Khaiduy/Open8_PCB/Open8_Epaper_demo_PCB/Pin_Assignment_RS6521_1_.xlsx

Sheet: Index
Index |  |  | 2021-11-05
No. | Sheet | Contents | Note
1 | Index | Table of contents of this Excel file | This sheet
2 | History | Modified history of this Excel file
3 | Chip Allocation | Chip Allocation
4 | Pin Assignment R4250 | Pin Assignment for R4250
5 | Pin Assignment R4251 | Pin Assignment for R4251
6 | Pin Assignment R4252 | Pin Assignment for R4252
7 | Circuit Layout | Circuit Layout
8 | IO Description | Description of I/O Pins

Sheet: History
Back to Index
 | Modified History
 | No. | Date | Modified by | Sheet | Updates | Note
 | 1 | 2017-06-15 | Hotta | All | New created
 | 2 | 2017-06-25 | Hotta | Chip Allocation Pin Assignment R4252 | Relocated HU_RISC16 => HU_FLOATW & HU_DCT32
 | 3 | 2017-06-26 | Hotta | Pin Assignment R4252 | No.74 => Unused
 | 4 | 2017-07-03 | Hotta | Pin Assignment R4252 | All pins have been relocated.
 | 5 | 2017-07-06 | Hotta | Pin Assignment R4252 | Common digital input pins have been assigned.
 | 6 | 2017-07-07 | Hotta | Pin Assignment R4252 | Relocated due to the cancellation of AESCOM.
 | 7 | 2017-07-07 | Hotta | Pin Assignment R4252 | Bug fix (No.12, 62, 82).
 | 8
 | 9
 | 10
 | 11
 | 12
 | 13
 | 14
 | 15
 | 16
 | 17
 | 18
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
