Khaiduy/Open8_PCB/PCB_20PIN_PMOD_ADAPTER/JTAG_PMOD_ADAPTER.png

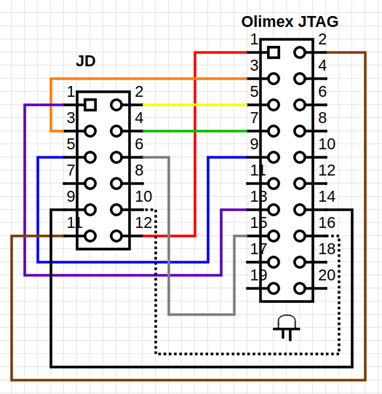
PCB_20PIN_PMOD_ADAPTER/JTAG_PMOD_ADAPTER.png
