Khaiduy/Open8_PCB/PCB_20PIN_PMOD_ADAPTER/Pmod_to_JTAG_bottom.png

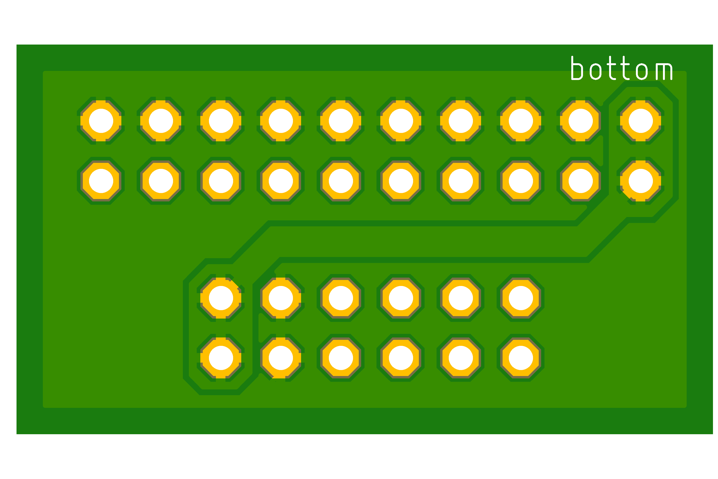
PCB_20PIN_PMOD_ADAPTER/Pmod_to_JTAG_bottom.png
