Khaiduy/Open8_PCB/PCB_20PIN_PMOD_ADAPTER/Pmod_to_JTAG_top.png

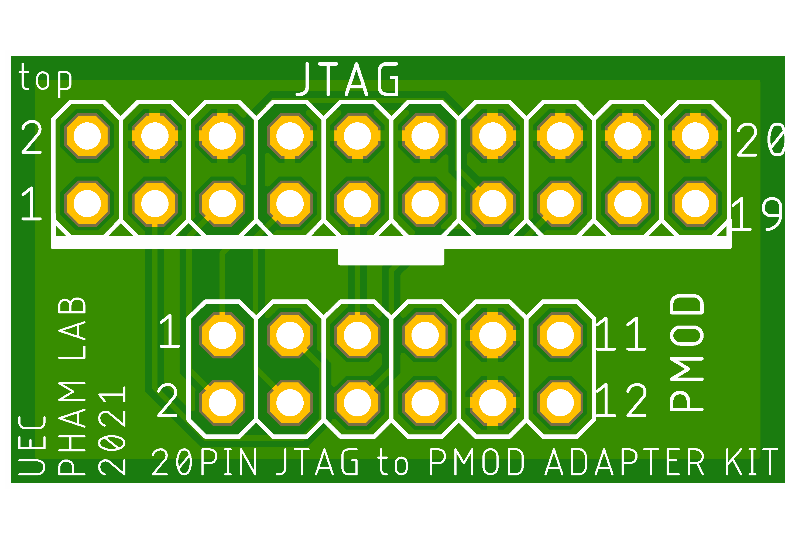
PCB_20PIN_PMOD_ADAPTER/Pmod_to_JTAG_top.png
