Khaiduy/Open8_PCB/PCB_ROHM_BaAnh/PCB_ROHM_BaAnh_bottom.png

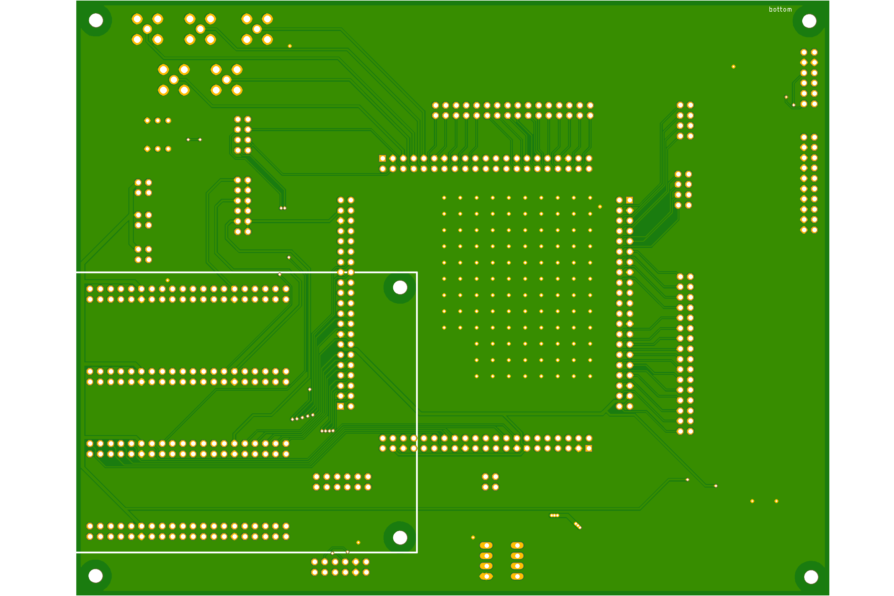
PCB_ROHM_BaAnh/PCB_ROHM_BaAnh_bottom.png
