Khaiduy/Open8_PCB/QFP160_new_socket/qfp160_socket_new_bottom.png

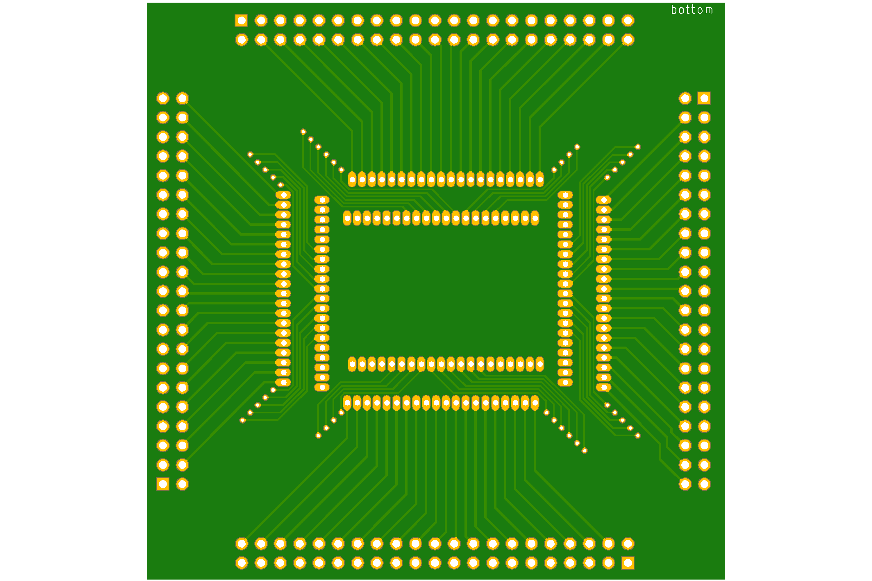
QFP160_new_socket/qfp160_socket_new_bottom.png
