Khaiduy/Open8_PCB/SERV_Open8_SOTB_PCB/serv_open8_sotb_bottom.png

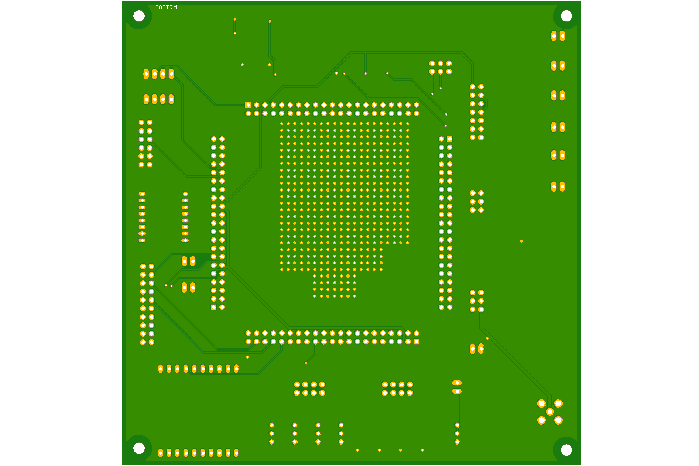
SERV_Open8_SOTB_PCB/serv_open8_sotb_bottom.png
