Khaiduy/Open8_PCB/TR4_PGA257(v4.0)/TR4.pdf

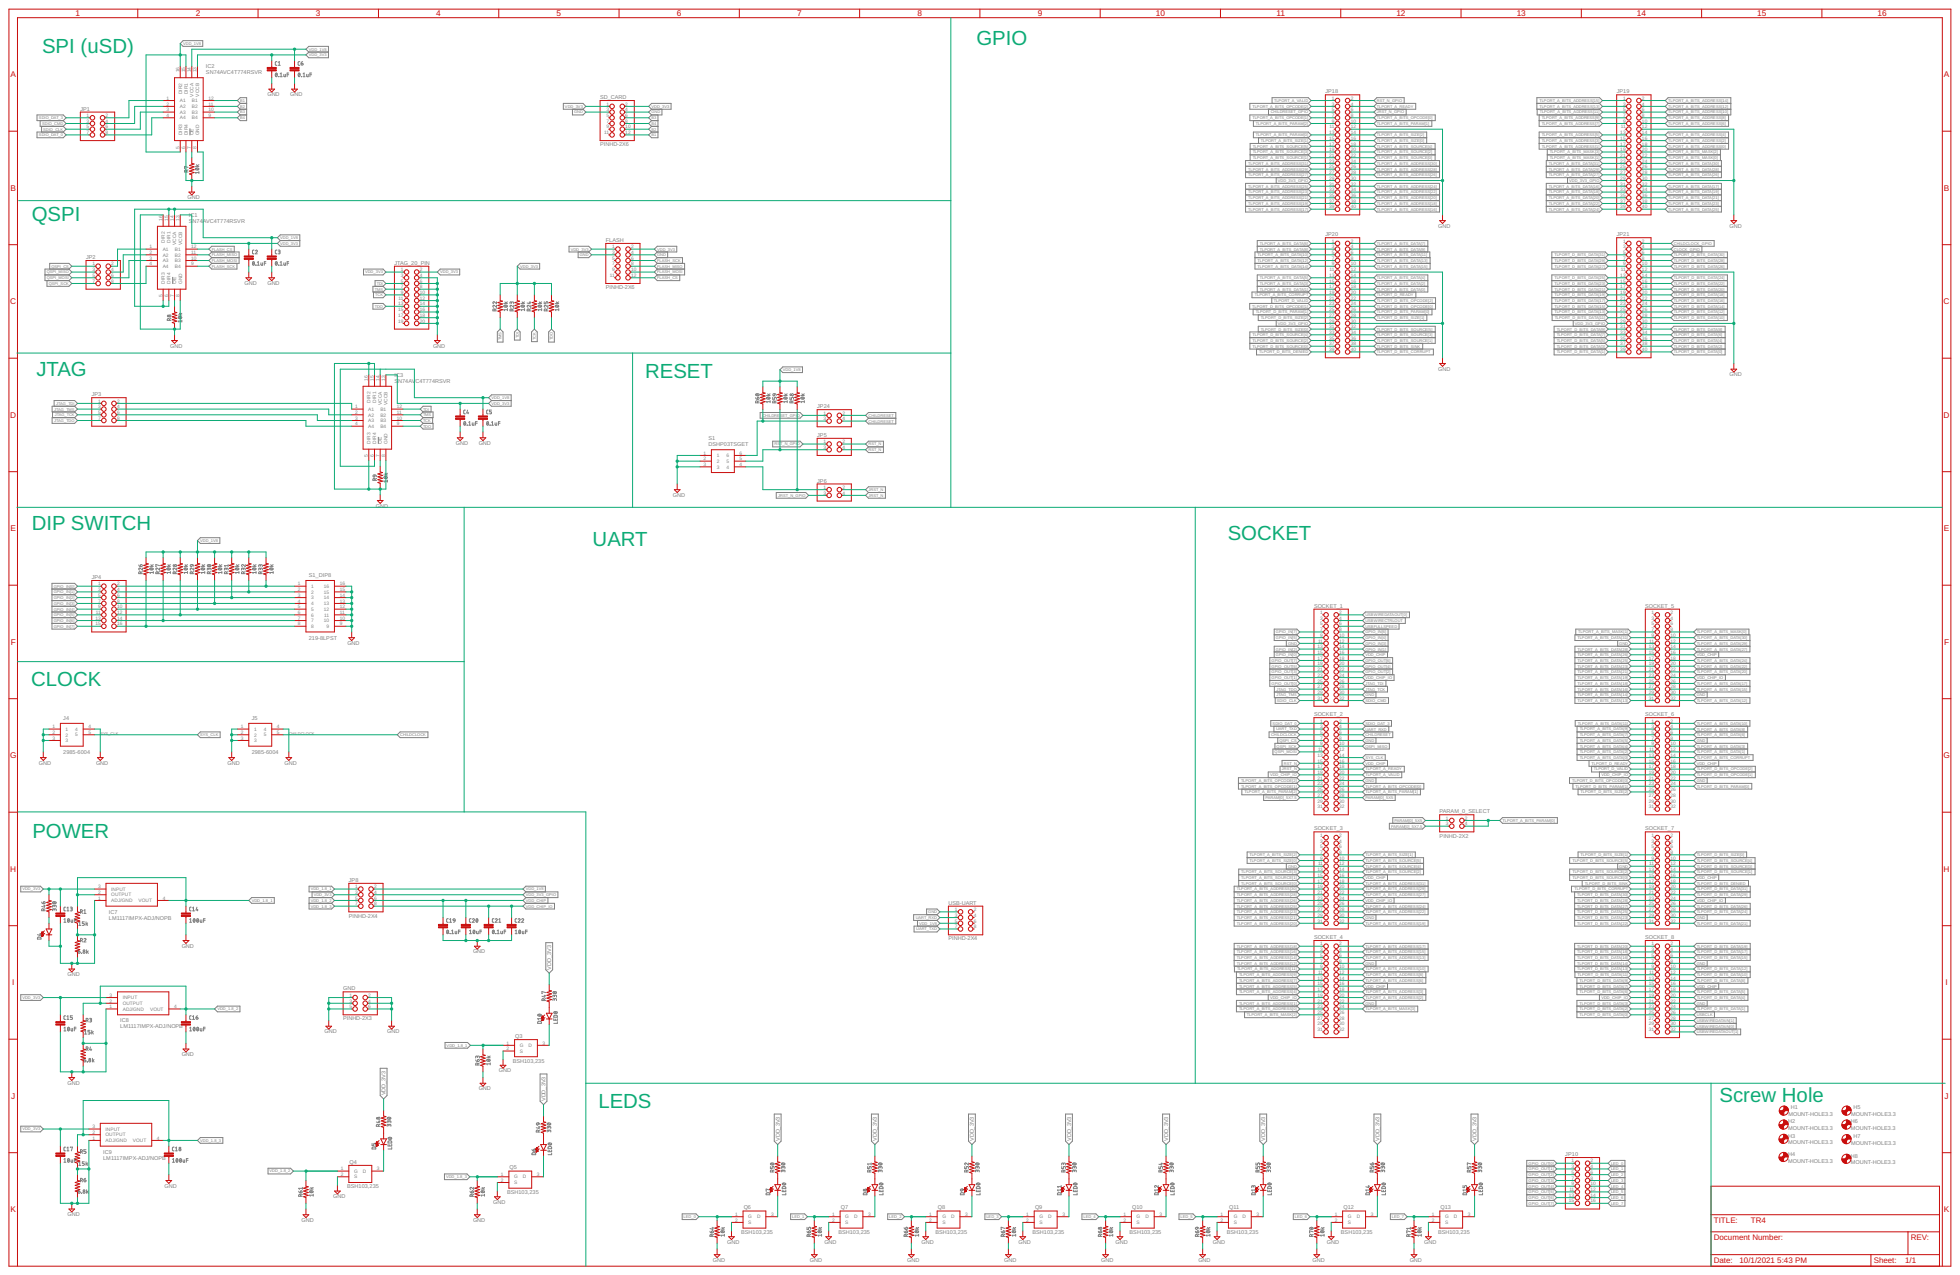
[picture p20: page 1]

MOUNT-HOLE3.3 MOUNT-HOLE3.3
