Khaiduy/Open8_PCB/SERV_Open8_TSMC_PCB/serv_open8_tsmc.pdf

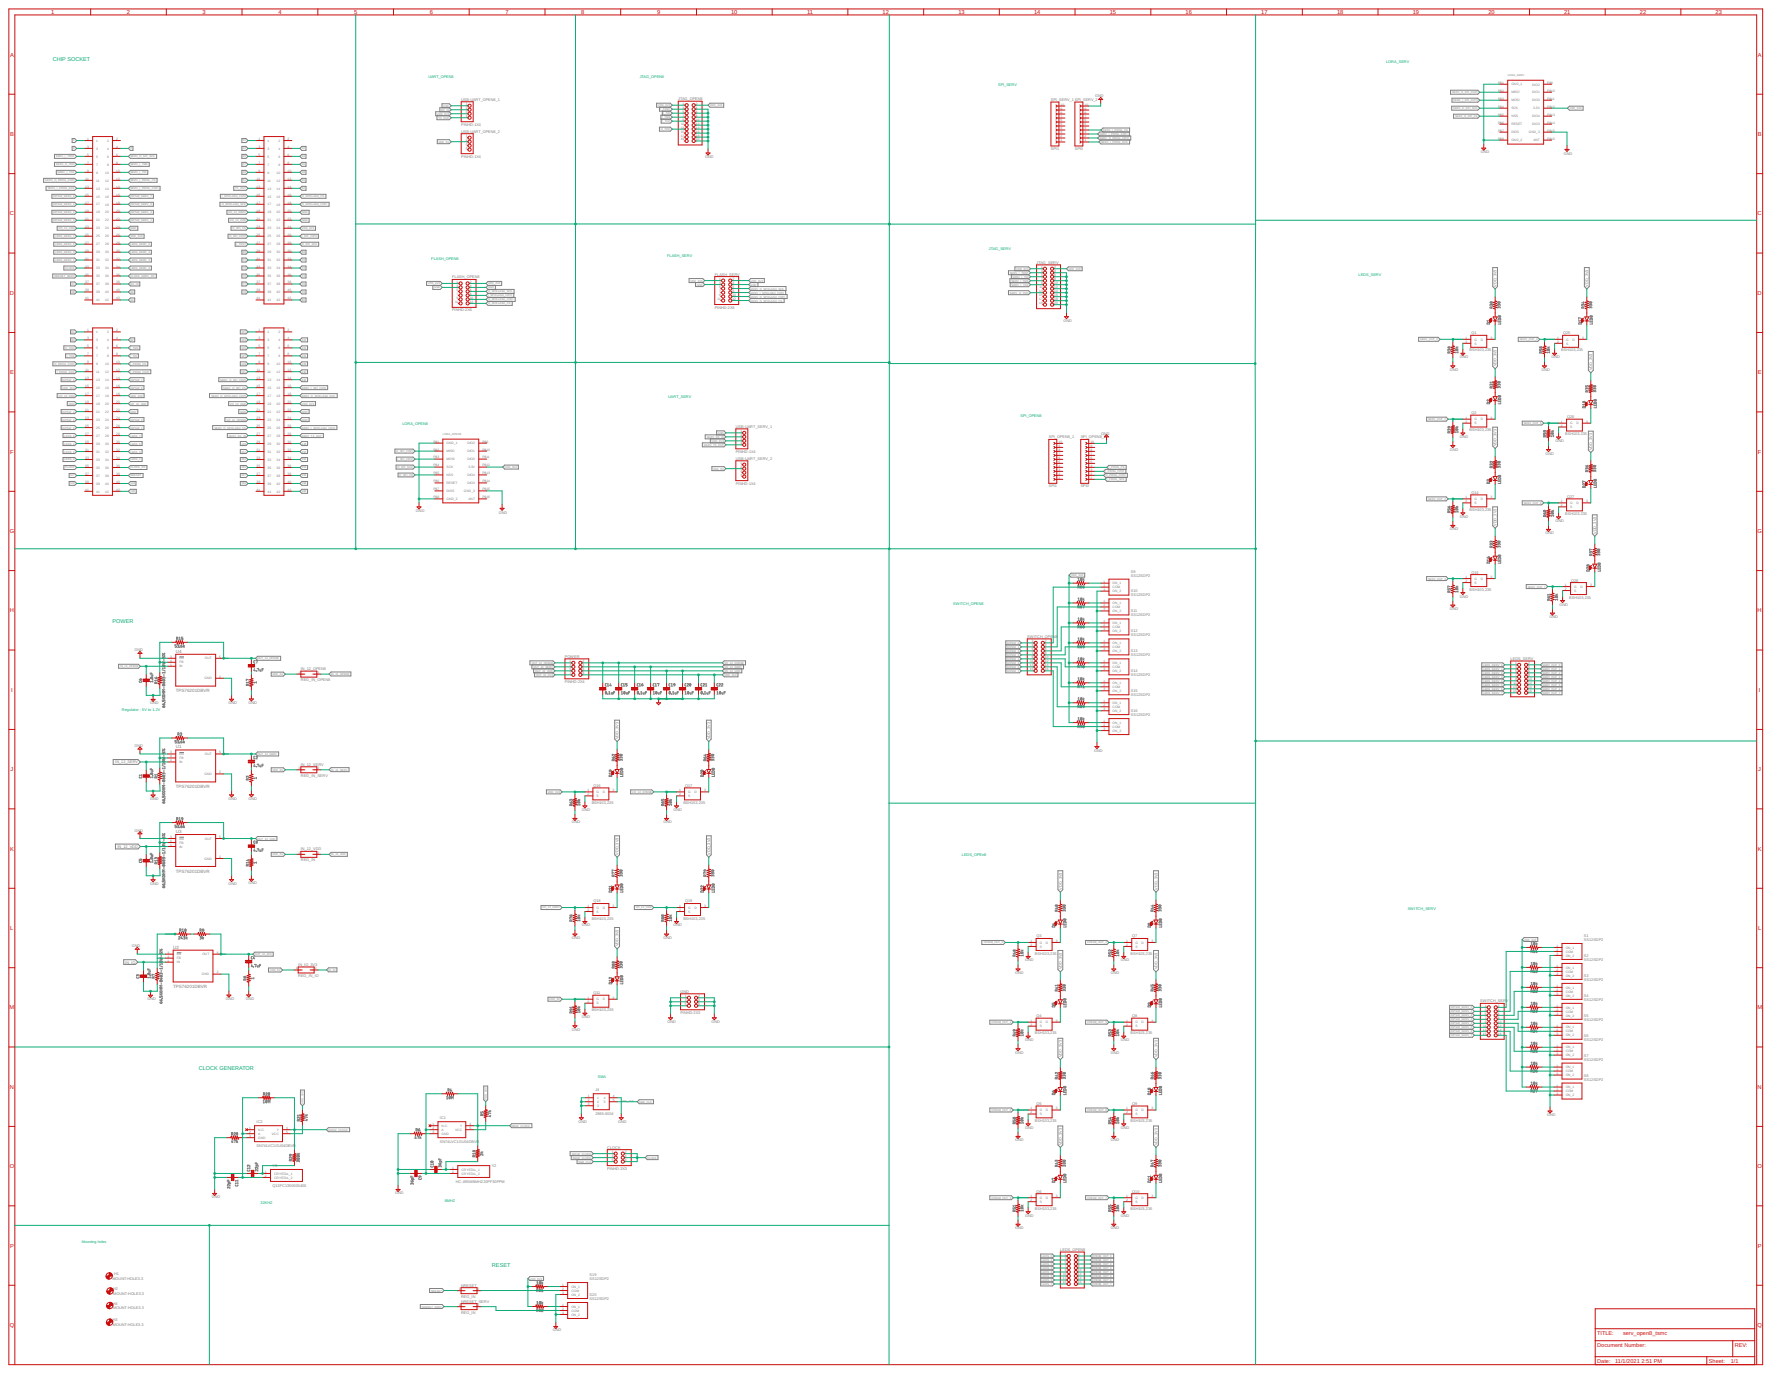
[picture p24: page 1]
