Khaiduy/Open8_PCB/TR4_PGA257(v4.0)/TEE_PGA257_v3.0.pdf

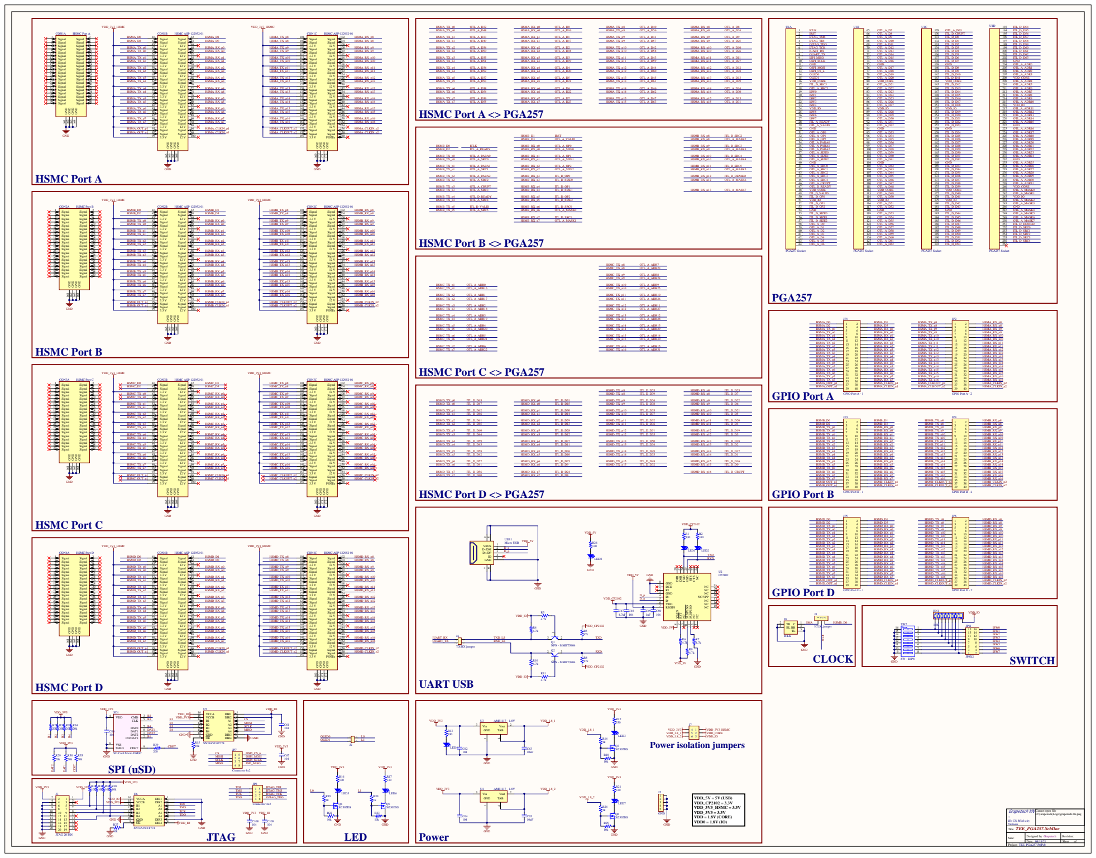
[picture p25: page 1]

NC 22 CTS 23 RTS 24 RXD 25 TXD 26 DSR 27 DTR 28

Cannot open file
D:\Grapetech\Logo\grapetech-06.png

Date: 04/19/21 | Sheet of
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
