Khaiduy/Open8_PCB/SERV_Open8_TSMC_PCB/serv_open8_tsmc.brd

## EAGLE design SERV_Open8_TSMC_PCB/serv_open8_tsmc.brd (2021-11-15)

Schematic: serv_open8_tsmc.sch

Parts:
C1, C3, C5, C6: 1.0uF; 0603
C2, C4, C7, C8: 4.7uF; 0603
C9, C10: 36pF; 0603
C11, C12: 22pF; 0603
C14, C16, C19, C21: 0.1uF; 0603
C15, C17, C20, C22: 10uF; 0603
CLOCK: PINHD-2X3; 2X03
D1, D2, D3, D4, D5, D6, D7, D8, D9, D10, D11, D12, D16, D17, D18, D19, D20, D21, D22, D27, D28: LED0; LED-0603
FLASH_OPEN8: PINHD-2X6; 2X06
FLASH_SERV: PINHD-2X6; 2X06
GND: PINHD-2X3; 2X03
H1, H2, H3, H4: MOUNT-HOLE3.3; 3,3
IC1, IC2: SN74LVC1GU04DBVR; SOT95P280X145-5N
IN_12_OPEN8: REG_IN_OPEN8; JP1
IN_12_SERV: REG_IN_SERV; JP1
IN_12_VDD: REG_IN; JP1
IN_IO_3V3: REG_IN_IO; JP1
J4: 2985-6004; 29856004
JTAG_OPEN8: PINHD-2X10; 2X10
JTAG_SERV: PINHD-2X10; 2X10
LEDS_OPEN8: PINHD-2X8; 2X08
LEDS_SERV: PINHD-2X8; 2X08
LORA_OPEN8: RFM95W-915S2; RFM95-915S2
LORA_SERV: RFM95W-915S2; RFM95-915S2
NRESET: REG_IN; JP1
NRESET_SERV: REG_IN; JP1
POWER: PINHD-2X4; 2X04
Q1, Q2, Q3, Q4, Q5, Q6, Q7, Q8, Q9, Q10, Q11, Q14, Q15, Q16, Q17, Q18, Q19, Q25, Q26, Q27, Q28: BSH103,235; SOT95P230X110-3N
R1, R7, R13, R16: 66.5KOHM-0603-1/10W-5%; 0603
R2, R8, R14, R17: 1; 0603
R3, R15, R19: 53.6k; 0603
R4, R20: 10M; 0603
R5, R6, R21, R28: 47k; 0603
R9: 3k; 0603
R10: 243k; 0603
R11, R12, R22, R23, R24, R25, R26, R27, R38, R39, R48, R49, R50, R51, R52, R53, R54, R55, R56, R57, R58, R59, R60, R61, R63, R65, R66, R67, R68, R69, R70, R71, R78, R80, R81, R82, R89, R90, R91: 10k; 0603
R18: 2k; 0603
R29: 300k; 0603
R30, R31, R32, R33, R34, R35, R36, R37, R40, R41, R42, R43, R44, R45, R46, R47, R62, R64, R77, R79, R88: 330; 0603
S1, S2, S3, S4, S5, S6, S7, S8, S9, S10, S11, S12, S13, S14, S15, S16, S19, S20: SS12SDP2
SPI_OPEN8_1: SPI1; FE10
SPI_OPEN8_2: SPI0; FE10
SPI_SERV_1: SPI1; FE10
SPI_SERV_2: SPI0; FE10
SWITCH_OPEN8: PINHD-2X8; 2X08
SWITCH_SERV: PINHD-2X8; 2X08
U1, U2, U3, U4: TPS76201DBVR; SOT95P280X145-5N
U$1, U$2, U$3, U$4: 2X41_HEADER
USB-UART_OPEN8_1, USB-UART_OPEN8_2: PINHD-1X4; 1X04
USB-UART_SERV_1, USB-UART_SERV_2: PINHD-1X4; 1X04
Y2: HC-49SM8MHZ20PF30PPM; HC49SM8MHZ20PF30PPM
Y3: Q13FC1350000400

Connections:
1: U$1.1
2: U$1.4
3: U$1.3
8MHZ_CLOCK: CLOCK.3, IC1.4 (Y), R4.2, R18.2
32KHZ_CLOCK: CLOCK.1, IC2.4 (Y), R20.2, R29.2
37: U$1.37
38: U$1.40
39: U$1.39
40: U$1.42
41: U$2.1
42: U$2.4
43: U$2.3
44: U$2.6
45: U$2.5
46: U$2.8
47: U$2.7
48: U$2.10
49: U$2.9
50: U$2.12
51: U$2.11
52: U$2.14
68: U$2.30
69: U$2.29
70: U$2.32
71: U$2.31
72: U$2.34
73: U$2.33
74: U$2.36
75: U$2.35
76: U$2.38
77: U$2.37
78: U$2.40
79: U$2.39
80: U$2.42
81: U$3.1
82: U$3.4
83: U$3.3
117: U$3.37
118: U$3.40
119: U$3.39
120: U$3.42
121: U$4.1
122: U$4.4
123: U$4.3
124: U$4.6
125: U$4.5
126: U$4.8
127: U$4.7
128: U$4.10
129: U$4.9
130: U$4.12
131: U$4.11
132: U$4.14
148: U$4.30
149: U$4.29
150: U$4.32
151: U$4.31
152: U$4.34
153: U$4.33
154: U$4.36
155: U$4.35
156: U$4.38
157: U$4.37
158: U$4.40
159: U$4.39
160: U$4.42
CLOCK: CLOCK.2, CLOCK.4, CLOCK.6, U$1.33, U$3.35
CLOCK_SERV_XO: U$1.36
CLOCK_XO: U$3.36
DIPSW_0: SWITCH_OPEN8.1, U$3.25
DIPSW_1: SWITCH_OPEN8.3, U$3.26
DIPSW_2: SWITCH_OPEN8.5, U$3.23
DIPSW_3: SWITCH_OPEN8.7, U$3.24
DIPSW_4: SWITCH_OPEN8.9, U$3.21
DIPSW_5: SWITCH_OPEN8.11, U$3.16
DIPSW_6: SWITCH_OPEN8.13, U$3.13
DIPSW_7: SWITCH_OPEN8.15, U$3.14
DIPSW_SERV_0: SWITCH_SERV.1, U$1.21
DIPSW_SERV_1: SWITCH_SERV.3, U$1.22
DIPSW_SERV_2: SWITCH_SERV.5, U$1.19
DIPSW_SERV_3: SWITCH_SERV.7, U$1.20
DIPSW_SERV_4: SWITCH_SERV.9, U$1.17
DIPSW_SERV_5: SWITCH_SERV.11, U$1.18
DIPSW_SERV_6: SWITCH_SERV.13, U$1.15
DIPSW_SERV_7: SWITCH_SERV.15, U$1.16
GND: C1.2, C3.2, C5.2, C6.2, C9.2, C10.1, C11.2, C12.1, C14.2, C15.2, C16.2, C17.2, C19.2, C20.2, C21.2, C22.2, FLASH_OPEN8.3, FLASH_OPEN8.4, FLASH_SERV.3, FLASH_SERV.4, GND.1, GND.2, GND.3, GND.4, GND.5, GND.6, J4.1, J4.2, J4.3, J4.4, JTAG_OPEN8.4, JTAG_OPEN8.6, JTAG_OPEN8.8, JTAG_OPEN8.10, JTAG_OPEN8.12, JTAG_OPEN8.14, JTAG_OPEN8.16, JTAG_OPEN8.18, JTAG_OPEN8.20, JTAG_SERV.4, JTAG_SERV.6, JTAG_SERV.8, JTAG_SERV.10, JTAG_SERV.12, JTAG_SERV.14, JTAG_SERV.16, JTAG_SERV.18, JTAG_SERV.20, LORA_OPEN8.P$1 (GND_1), LORA_OPEN8.P$8 (GND_2), LORA_OPEN8.P$15 (GND_3), LORA_SERV.P$1 (GND_1), LORA_SERV.P$8 (GND_2), LORA_SERV.P$15 (GND_3), Q1.2 (S), Q2.2 (S), Q3.2 (S), Q4.2 (S), Q5.2 (S), Q6.2 (S), Q7.2 (S), Q8.2 (S), Q9.2 (S), Q10.2 (S), Q11.2 (S), Q14.2 (S), Q15.2 (S), Q16.2 (S), Q17.2 (S), Q18.2 (S), Q19.2 (S), Q25.2 (S), Q26.2 (S), Q27.2 (S), Q28.2 (S), R1.1, R2.1, R6.1, R7.1, R8.1, R13.1, R14.1, R16.1, R17.1, R28.1, R38.1, R39.1, R48.1, R49.1, R50.1, R51.1, R52.1, R53.1, R54.1, R55.1, R56.1, R57.1, R58.1, R59.1, R60.1, R61.1, R63.1, R65.1, R78.1, R80.1, R91.1, S1.3 (ON_2), S2.3 (ON_2), S3.3 (ON_2), S4.3 (ON_2), S5.3 (ON_2), S6.3 (ON_2), S7.3 (ON_2), S8.3 (ON_2), S9.3 (ON_2), S10.3 (ON_2), S11.3 (ON_2), S12.3 (ON_2), S13.3 (ON_2), S14.3 (ON_2), S15.3 (ON_2), S16.3 (ON_2), S19.3 (ON_2), S20.3 (ON_2), SPI_OPEN8_2.10, SPI_SERV_2.10, U1.2 (GND), U1.3 (!EN), U2.2 (GND), U2.3 (!EN), U3.2 (GND), U3.3 (!EN), U4.2 (GND), U4.3 (!EN), U$1.24, U$2.20, U$2.22, U$3.19, U$3.22, U$4.21, U$4.22, U$4.24, USB-UART_OPEN8_1.1, USB-UART_SERV_1.1
IN_12_OPEN8: C6.1, IN_12_OPEN8.2, U4.1 (IN)
IN_12_SERV: C1.1, IN_12_SERV.2, U1.1 (IN)
IN_12_VDD: C5.1, IN_12_VDD.2, U3.1 (IN)
IN_IO: C3.1, IN_IO_3V3.2, U2.1 (IN)
I_PROG_COPI: SPI_OPEN8_2.3, U$3.12
I_PROG_CS: SPI_OPEN8_2.4, U$3.10
I_PROG_SCK: SPI_OPEN8_2.1, U$3.11
I_SPIFLASH_CIPO: FLASH_OPEN8.8, U$2.15
I_SPI_CIPO: LORA_OPEN8.P$3 (MOSI), U$2.26
I_TCK: JTAG_OPEN8.9, U$3.7
I_TDI: JTAG_OPEN8.5, U$3.8
I_TMS: JTAG_OPEN8.7, U$3.6
I_TRST: JTAG_OPEN8.3, U$2.27
LEDS_0: LEDS_OPEN8.1, U$3.33
LEDS_1: LEDS_OPEN8.3, U$3.34
LEDS_2: LEDS_OPEN8.5, U$3.31
LEDS_3: LEDS_OPEN8.7, U$3.32
LEDS_4: LEDS_OPEN8.9, U$3.29
LEDS_5: LEDS_OPEN8.11, U$3.30
LEDS_6: LEDS_OPEN8.13, U$3.27
LEDS_7: LEDS_OPEN8.15, U$3.28
LEDS_SERV_0: LEDS_SERV.1, U$1.34
LEDS_SERV_1: LEDS_SERV.3, U$1.31
LEDS_SERV_2: LEDS_SERV.5, U$1.32
LEDS_SERV_3: LEDS_SERV.7, U$1.29
LEDS_SERV_4: LEDS_SERV.9, U$1.30
LEDS_SERV_5: LEDS_SERV.11, U$1.27
LEDS_SERV_6: LEDS_SERV.13, U$1.28
LEDS_SERV_7: LEDS_SERV.15, U$1.25
unnamed: R1.2, R3.1, U1.4 (FB)
unnamed: C2.2, R2.2
unnamed: NRESET.2, S19.2 (COM)
unnamed: IC1.3 (GND), R6.2
unnamed: C9.1, IC1.2 (A), R4.1, Y2.2 (CRYSTAL_2)
unnamed: R7.2, R10.1, U2.4 (FB)
unnamed: C4.2, R8.2
unnamed: R9.1, R10.2
unnamed: C10.2, R18.1, Y2.1 (CRYSTAL_1)
unnamed: R11.1, S1.1 (ON_1)
unnamed: R12.1, S2.1 (ON_1)
unnamed: R13.2, R19.1, U3.4 (FB)
unnamed: C8.2, R14.2
unnamed: IC1.5 (VCC), R5.1
unnamed: D12.A, R88.1
unnamed: R22.1, S3.1 (ON_1)
unnamed: R23.1, S4.1 (ON_1)
unnamed: R24.1, S5.1 (ON_1)
unnamed: R25.1, S6.1 (ON_1)
unnamed: R26.1, S7.1 (ON_1)
unnamed: R27.1, S8.1 (ON_1)
unnamed: S5.2 (COM), SWITCH_SERV.10
unnamed: S6.2 (COM), SWITCH_SERV.12
unnamed: S7.2 (COM), SWITCH_SERV.14
unnamed: S8.2 (COM), SWITCH_SERV.16
unnamed: S4.2 (COM), SWITCH_SERV.8
unnamed: S3.2 (COM), SWITCH_SERV.6
unnamed: S2.2 (COM), SWITCH_SERV.4
unnamed: S1.2 (COM), SWITCH_SERV.2
unnamed: R15.1, R16.2, U4.4 (FB)
unnamed: IC2.3 (GND), R28.2
unnamed: C7.2, R17.2
unnamed: C11.1, IC2.2 (A), R20.1, Y3.2 (CRYSTAL_2)
unnamed: C12.2, R29.1, Y3.1 (CRYSTAL_1)
unnamed: NRESET_SERV.2, S20.2 (COM)
unnamed: IC2.5 (VCC), R21.1
unnamed: D1.A, R30.1
unnamed: D1.C, Q1.3 (D)
unnamed: D2.A, R31.1
unnamed: D2.C, Q2.3 (D)
unnamed: R81.1, S19.1 (ON_1)
unnamed: R82.1, S20.1 (ON_1)
unnamed: D12.C, Q11.3 (D)
unnamed: D3.A, R32.1
unnamed: D3.C, Q14.3 (D)
unnamed: D4.A, R40.1
unnamed: D4.C, Q3.3 (D)
unnamed: D5.A, R41.1
unnamed: D16.A, R33.1
unnamed: D16.C, Q15.3 (D)
unnamed: D17.A, R34.1
unnamed: D17.C, Q25.3 (D)
unnamed: D18.A, R35.1
unnamed: D18.C, Q26.3 (D)
unnamed: D27.A, R36.1
unnamed: D27.C, Q27.3 (D)
unnamed: D28.A, R37.1
unnamed: D28.C, Q28.3 (D)
unnamed: D19.A, R62.1
unnamed: D5.C, Q4.3 (D)
unnamed: D6.A, R42.1
unnamed: D6.C, Q5.3 (D)
unnamed: D7.A, R43.1
unnamed: D7.C, Q6.3 (D)
unnamed: D8.A, R44.1
unnamed: D8.C, Q7.3 (D)
unnamed: D9.A, R45.1
unnamed: D19.C, Q16.3 (D)
unnamed: D20.A, R64.1
unnamed: D20.C, Q17.3 (D)
unnamed: D21.A, R77.1
unnamed: D21.C, Q18.3 (D)
unnamed: D22.A, R79.1
unnamed: D22.C, Q19.3 (D)
unnamed: D9.C, Q8.3 (D)
unnamed: D10.A, R46.1
unnamed: D10.C, Q9.3 (D)
unnamed: D11.A, R47.1
unnamed: D11.C, Q10.3 (D)
unnamed: R66.1, S9.1 (ON_1)
unnamed: R67.1, S10.1 (ON_1)
unnamed: R68.1, S11.1 (ON_1)
unnamed: R69.1, S12.1 (ON_1)
unnamed: R70.1, S13.1 (ON_1)
unnamed: R71.1, S14.1 (ON_1)
unnamed: R89.1, S15.1 (ON_1)
unnamed: R90.1, S16.1 (ON_1)
unnamed: S13.2 (COM), SWITCH_OPEN8.10
unnamed: S14.2 (COM), SWITCH_OPEN8.12
unnamed: S15.2 (COM), SWITCH_OPEN8.14
unnamed: S16.2 (COM), SWITCH_OPEN8.16
unnamed: S12.2 (COM), SWITCH_OPEN8.8
unnamed: S11.2 (COM), SWITCH_OPEN8.6
unnamed: S10.2 (COM), SWITCH_OPEN8.4
unnamed: S9.2 (COM), SWITCH_OPEN8.2
NRESET: NRESET.1, U$3.38
NRESET_SERV: NRESET_SERV.1, U$1.35
OPEN8_OUT_0: LEDS_OPEN8.2, Q3.1 (G), R48.2
OPEN8_OUT_1: LEDS_OPEN8.4, Q4.1 (G), R49.2
OPEN8_OUT_2: LEDS_OPEN8.6, Q5.1 (G), R50.2
OPEN8_OUT_3: LEDS_OPEN8.8, Q6.1 (G), R51.2
OPEN8_OUT_4: LEDS_OPEN8.10, Q7.1 (G), R52.2
OPEN8_OUT_5: LEDS_OPEN8.12, Q8.1 (G), R53.2
OPEN8_OUT_6: LEDS_OPEN8.14, Q9.1 (G), R54.2
OPEN8_OUT_7: LEDS_OPEN8.16, Q10.1 (G), R55.2
OUT_12_OPEN8: C7.1, POWER.1, R15.2, U4.5 (OUT)
OUT_12_SERV: C2.1, POWER.3, R3.2, U1.5 (OUT)
OUT_12_VDD: C8.1, POWER.5, R19.2, U3.5 (OUT)
OUT_IO_3V3: C4.1, POWER.7, R9.2, U2.5 (OUT)
O_PROG_CIPO: SPI_OPEN8_2.2, U$3.9
O_SPIFLASH_COPI: FLASH_OPEN8.10, U$2.18
O_SPIFLASH_CS: FLASH_OPEN8.12, U$2.16
O_SPIFLASH_SCK: FLASH_OPEN8.6, U$2.17
O_SPI_COPI: LORA_OPEN8.P$2 (MISO), U$2.25
O_SPI_CS: LORA_OPEN8.P$5 (NSS), U$2.23
O_SPI_SCK: LORA_OPEN8.P$4 (SCK), U$2.28
O_TDO: JTAG_OPEN8.13, U$3.5
RX_IN: U$1.38, USB-UART_OPEN8_1.2
SERV_I_PROG_COPI: SPI_SERV_2.3, U$1.14
SERV_I_PROG_CS: SPI_SERV_2.4, U$1.12
SERV_I_PROG_SCK: SPI_SERV_2.1, U$1.13
SERV_I_SPIFLASH_CIPO: FLASH_SERV.8, U$4.26
SERV_I_SPI_CIPO: LORA_SERV.P$3 (MOSI), U$4.16
SERV_I_TCK: JTAG_SERV.9, U$1.9
SERV_I_TDI: JTAG_SERV.5, U$1.10
SERV_I_TMS: JTAG_SERV.7, U$1.8
SERV_I_TRST: JTAG_SERV.3, U$1.5
SERV_OUT_0: LEDS_SERV.2, Q1.1 (G), R38.2
SERV_OUT_1: LEDS_SERV.4, Q2.1 (G), R39.2
SERV_OUT_2: LEDS_SERV.6, Q14.1 (G), R56.2
SERV_OUT_3: LEDS_SERV.8, Q15.1 (G), R57.2
SERV_OUT_4: LEDS_SERV.10, Q25.1 (G), R58.2
SERV_OUT_5: LEDS_SERV.12, Q26.1 (G), R59.2
SERV_OUT_6: LEDS_SERV.14, Q27.1 (G), R60.2
SERV_OUT_7: LEDS_SERV.16, Q28.1 (G), R61.2
SERV_O_PROG_CIPO: SPI_SERV_2.2, U$1.11
SERV_O_SPIFLASH_COPI: FLASH_SERV.10, U$4.17
SERV_O_SPIFLASH_CS: FLASH_SERV.12, U$4.25
SERV_O_SPIFLASH_SCK: FLASH_SERV.6, U$4.18
SERV_O_SPI_COPI: LORA_SERV.P$2 (MISO), U$4.13
SERV_O_SPI_CS: LORA_SERV.P$5 (NSS), U$4.15
SERV_O_SPI_SCK: LORA_SERV.P$4 (SCK), U$1.6
SERV_O_TDO: JTAG_SERV.13, U$1.7
SERV_RX_IN: U$4.27, USB-UART_SERV_1.2
SERV_TX_OUT: U$4.28, USB-UART_SERV_1.4
SMA_CLK: CLOCK.5, J4.5
TX_OUT: U$2.13, USB-UART_OPEN8_1.4
VDD_3V3: C21.1, C22.1, FLASH_OPEN8.1, FLASH_OPEN8.2, FLASH_SERV.1, FLASH_SERV.2, JTAG_OPEN8.1, JTAG_OPEN8.2, JTAG_SERV.1, JTAG_SERV.2, LORA_OPEN8.P$12 (3.3V), LORA_SERV.P$12 (3.3V), POWER.8, Q16.1 (G), R5.2, R11.2, R12.2, R21.2, R22.2, R23.2, R24.2, R25.2, R26.2, R27.2, R30.2, R31.2, R32.2, R33.2, R34.2, R35.2, R36.2, R37.2, R40.2, R41.2, R42.2, R43.2, R44.2, R45.2, R46.2, R47.2, R62.2, R63.2, R64.2, R66.2, R67.2, R68.2, R69.2, R70.2, R71.2, R77.2, R79.2, R81.2, R82.2, R88.2, R89.2, R90.2, U$1.26, U$2.24, U$3.15, U$3.18, U$4.20, USB-UART_OPEN8_1.3, USB-UART_SERV_1.3
VDD_5V: IN_12_OPEN8.1, IN_12_SERV.1, IN_12_VDD.1, IN_IO_3V3.1, Q11.1 (G), R91.2, USB-UART_OPEN8_2.2, USB-UART_SERV_2.2
VO_12_OPEN8: C14.1, C15.1, POWER.2, Q17.1 (G), R65.2, U$4.23
VO_12_SERV: C16.1, C17.1, POWER.4, Q18.1 (G), R78.2, U$2.19
VO_12_VDD: C19.1, C20.1, POWER.6, Q19.1 (G), R80.2, U$1.23, U$2.21, U$3.17, U$3.20, U$4.19

Notes on the sheet:
Regulator - 5V to 1.2V
CHIP SOCKET
POWER
CLOCK GENERATOR
RESET
Mounting holes
UART_OPEN8
FLASH_OPEN8
LORA_OPEN8
JTAG_OPEN8
FLASH_SERV
UART_SERV
SPI_SERV
JTAG_SERV
SPI_OPEN8
SWITCH_OPEN8
32KHZ
8MHZ
SMA
LEDS_OPEn8
SWITCH_SERV
LEDS_SERV
LORA_SERV

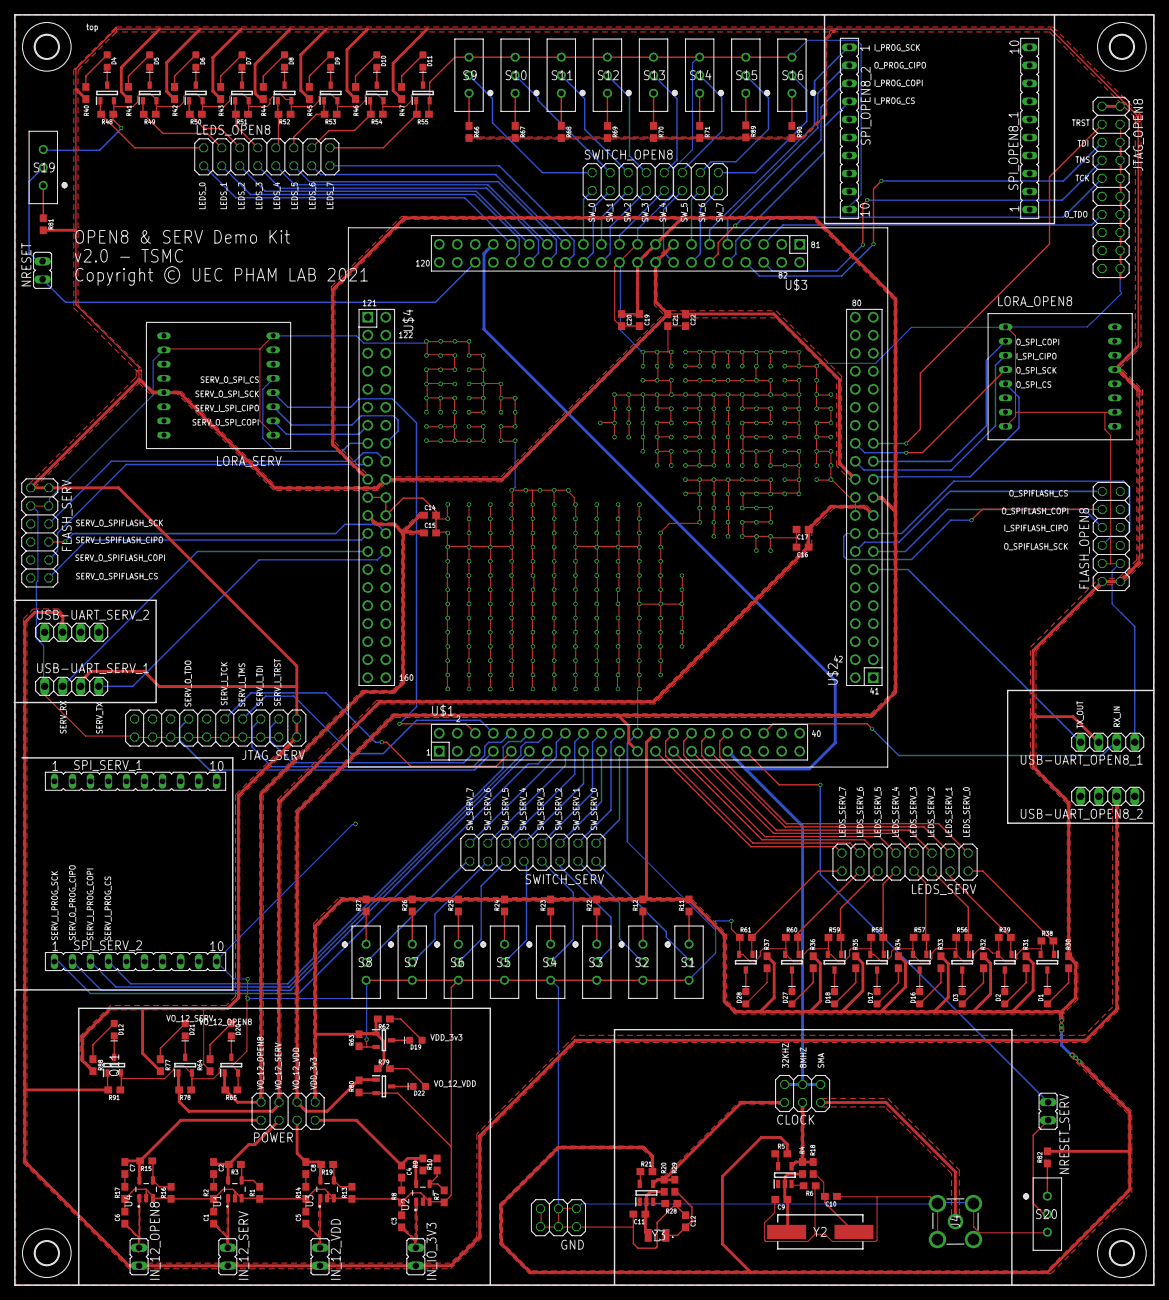
[picture p78: board serv_open8_tsmc.brd from above]

Board: 2 copper layers, 160.5 x 179.0 mm, 205 parts (0 on the bottom side), 201 nets.
