Khaiduy/Open8_PCB/SERV_Open8_ROHM_PCB/serv_open8_rohm.brd

## EAGLE design SERV_Open8_ROHM_PCB/serv_open8_rohm.brd (2021-11-15)

Schematic: serv_open8_rohm.sch

Parts:
C1, C3, C5, C6, C9, C11: 1.0uF; 0603
C2, C4, C7, C8, C10, C12: 4.7uF; 0603
C13, C14, C16, C19, C21, C23, C29, C30, C31, C32, C34, C35, C36, C37, C38, C39, C40, C41, C42, C43, C44: 0.1uF; 0603
C15, C17, C18, C20, C24: 10uF; 0603
C25, C26: 36pF; 0603
C27, C28: 22pF; 0603
CLOCK: PINHD-2X3; 2X03
D1, D2, D3, D4, D5, D19, D20, D21, D22: LED0; LED-0603
FLASH_OPEN8: PINHD-2X6; 2X06
FLASH_SERV: PINHD-2X6; 2X06
GND: PINHD-2X3; 2X03
H1, H2, H3, H4: MOUNT-HOLE3.3; 3,3
IC1, IC2: SN74LVC1GU04DBVR; SOT95P280X145-5N
IC3, IC4, IC5, IC6, IC7, IC8, IC10, IC11: TXB0108PWR; SOP65P640X120-20N
IN_3V3: REG_IN_IO; JP1
IN_OPEN8: REG_IN_OPEN8; JP1
IN_RAM: REG_IN_OPEN8; JP1
IN_SERV: REG_IN_SERV; JP1
IN_VDD: REG_IN; JP1
IN_VDDO: REG_IN_SERV; JP1
J4: 2985-6004; 29856004
JTAG_OPEN8: PINHD-2X10; 2X10
JTAG_SERV: PINHD-2X10; 2X10
LORA_OPEN8: RFM95W-915S2; RFM95-915S2
LORA_SERV: RFM95W-915S2; RFM95-915S2
MUX: PINHD-1X2; 1X02
NRESET_OPEN8: REG_IN; JP1
NRESET_SERV: REG_IN; JP1
OPEN8_FLASH, OPEN8_LORA, OPEN8_SPI: PINHD-2X4; 2X04
OPEN8_JTAG: PINHD-2X5; 2X05
OPEN8_LED: PINHD-1X2; 1X02
OPEN8_SW, OPEN8_UART: PINHD-2X2; 2X02
POWER: PINHD-2X6; 2X06
Q1, Q2, Q3, Q4, Q5, Q16, Q17, Q18, Q19: BSH103,235; SOT95P230X110-3N
R1, R4, R7, R11, R13, R16: 66.5KOHM-0603-1/10W-5%; 0603
R2, R5, R8, R12, R14, R17: 1; 0603
R3, R6, R15, R18, R19: 113k; 0603
R9: 3k; 0603
R10: 243k; 0603
R20, R22, R40, R52, R56, R62, R64, R77, R79: 330; 0603
R21, R23, R32, R33, R34, R39, R41, R48, R53, R54, R55, R57, R63, R65, R78, R80: 10k; 0603
R24, R28: 10M; 0603
R25, R26, R29, R30: 47k; 0603
R27: 2k; 0603
R31: 300k; 0603
S1, S2, S3, S4, S5, S6: SS12SDP2
SERV_FLASH: PINHD-2X4; 2X04
SERV_JTAG: PINHD-2X5; 2X05
SERV_LED: PINHD-1X2; 1X02
SERV_LORA: PINHD-2X4; 2X04
SERV_SPI: PINHD-2X4; 2X04
SERV_SW: PINHD-2X2; 2X02
SERV_UART: PINHD-2X2; 2X02
SPI_OPEN8_1: SPI1; FE10
SPI_OPEN8_2: SPI0; FE10
SPI_SERV_1: SPI0; FE10
SPI_SERV_2: SPI1; FE10
U1, U2, U3, U4, U5, U6: TPS76201DBVR; SOT95P280X145-5N
U$1, U$2, U$3, U$4: 2X41_HEADER
USB-UART_OPEN8_1, USB-UART_OPEN8_2: PINHD-1X4; 1X04
USB-UART_SERV_1, USB-UART_SERV_2: PINHD-1X4; 1X04
Y2: HC-49SM8MHZ20PF30PPM; HC49SM8MHZ20PF30PPM
Y3: Q13FC1350000400

Connections:
1: U$1.1
2: U$1.4
4: U$1.6
5: U$1.5
6: U$1.8
7: U$1.7
8: U$1.10
8MHZ_CLOCK: CLOCK.3, IC1.4 (Y), R24.2, R27.2
9: U$1.9
10: U$1.12
11: U$1.11
12: U$1.14
14: U$1.16
15: U$1.15
16: U$1.18
17: U$1.17
18: U$1.20
19: U$1.19
20: U$1.22
21: U$1.21
22: U$1.24
23: U$1.23
24: U$1.26
25: U$1.25
26: U$1.28
28: U$1.30
29: U$1.29
30: U$1.32
31: U$1.31
32: U$1.34
32KHZ_CLOCK: CLOCK.1, IC2.4 (Y), R28.2, R31.2
33: U$1.33
34: U$1.36
35: U$1.35
36: U$1.38
38: U$1.40
39: U$1.39
40: U$1.42
41: U$2.1
42: U$2.4
44: U$2.6
45: U$2.5
46: U$2.8
47: U$2.7
48: U$2.10
49: U$2.9
50: U$2.12
51: U$2.11
52: U$2.14
54: U$2.16
55: U$2.15
56: U$2.18
57: U$2.17
58: U$2.20
59: U$2.19
60: U$2.22
67: U$2.27
78: U$2.40
79: U$2.39
80: U$2.42
81: U$3.1
82: U$3.4
84: U$3.6
93: U$3.13
107: U$3.27
118: U$3.40
119: U$3.39
120: U$3.42
121: U$4.1
122: U$4.4
124: U$4.6
135: U$4.15
139: U$4.19
140: U$4.22
141: U$4.21
142: U$4.24
143: U$4.23
144: U$4.26
145: U$4.25
146: U$4.28
148: U$4.30
149: U$4.29
150: U$4.32
151: U$4.31
152: U$4.34
153: U$4.33
154: U$4.36
155: U$4.35
156: U$4.38
158: U$4.40
159: U$4.39
160: U$4.42
DR_CLOCK: CLOCK.2, CLOCK.4, CLOCK.6, U$2.28
DR_MUX: MUX.1, R34.2, U$3.23
DR_OPEN8_DIPSW_0: OPEN8_SW.1, U$3.11
DR_OPEN8_DIPSW_1: OPEN8_SW.3, U$3.14
DR_OPEN8_JTAG_TCK: OPEN8_JTAG.7, U$2.38
DR_OPEN8_JTAG_TDI: OPEN8_JTAG.1, U$3.5
DR_OPEN8_JTAG_TDO: OPEN8_JTAG.3, U$3.8
DR_OPEN8_JTAG_TMS: OPEN8_JTAG.9, U$2.35
DR_OPEN8_JTAG_TRST: OPEN8_JTAG.5, U$3.18
DR_OPEN8_LED_0: OPEN8_LED.1, U$3.7
DR_OPEN8_PSPI_CS: OPEN8_SPI.3, U$3.19
DR_OPEN8_PSPI_MISO: OPEN8_SPI.7, U$3.17
DR_OPEN8_PSPI_MOSI: OPEN8_SPI.5, U$3.20
DR_OPEN8_PSPI_SCK: OPEN8_SPI.1, U$3.22
DR_OPEN8_RESET: NRESET_OPEN8.1, U$2.30
DR_OPEN8_SPIFLASH_CIPO: OPEN8_FLASH.1, U$3.16
DR_OPEN8_SPIFLASH_COPI: OPEN8_FLASH.5, U$3.9
DR_OPEN8_SPIFLASH_CS: OPEN8_FLASH.3, U$3.12
DR_OPEN8_SPIFLASH_SCK: OPEN8_FLASH.7, U$3.10
DR_OPEN8_SPI_CS: OPEN8_LORA.3, U$2.33
DR_OPEN8_SPI_MISO: OPEN8_LORA.7, U$2.31
DR_OPEN8_SPI_MOSI: OPEN8_LORA.5, U$2.34
DR_OPEN8_SPI_SCK: OPEN8_LORA.1, U$2.36
DR_OPEN8_UART_RXD: OPEN8_UART.3, U$2.29
DR_OPEN8_UART_TXD: OPEN8_UART.1, U$2.32
DR_OPEN8_VDD: C13.1, C18.1, POWER.10, Q16.1 (G), R63.2, U$2.23
DR_RAM_VDD: C23.1, C24.1, POWER.12, Q2.1 (G), R23.2, U$2.21
DR_SERV_DIPSW_0: SERV_SW.1, U$4.9
DR_SERV_DIPSW_1: SERV_SW.3, U$4.12
DR_SERV_JTAG_TCK: SERV_JTAG.7, U$3.36
DR_SERV_JTAG_TDI: SERV_JTAG.5, U$3.35
DR_SERV_JTAG_TDO: SERV_JTAG.3, U$3.38
DR_SERV_JTAG_TMS: SERV_JTAG.9, U$3.33
DR_SERV_JTAG_TRST: SERV_JTAG.1, U$4.14
DR_SERV_LED_0: SERV_LED.1, U$4.5
DR_SERV_PSPI_CS: SERV_SPI.3, U$4.17
DR_SERV_PSPI_MISO: SERV_SPI.7, U$4.16
DR_SERV_PSPI_MOSI: SERV_SPI.5, U$4.18
DR_SERV_PSPI_SCK: SERV_SPI.1, U$4.20
DR_SERV_RESET: NRESET_SERV.1, U$3.26
DR_SERV_SPIFLASH_CIPO: SERV_FLASH.1, U$4.11
DR_SERV_SPIFLASH_COPI: SERV_FLASH.5, U$4.7
DR_SERV_SPIFLASH_CS: SERV_FLASH.3, U$4.8
DR_SERV_SPIFLASH_SCK: SERV_FLASH.7, U$4.10
DR_SERV_SPI_CS: SERV_LORA.3, U$3.31
DR_SERV_SPI_MISO: SERV_LORA.7, U$3.29
DR_SERV_SPI_MOSI: SERV_LORA.5, U$3.32
DR_SERV_SPI_SCK: SERV_LORA.1, U$3.34
DR_SERV_UART_RXD: SERV_UART.1, U$3.28
DR_SERV_UART_TXD: SERV_UART.3, U$3.30
DR_SERV_VDD: C14.1, C15.1, POWER.8, Q17.1 (G), R65.2, U$3.21
GND: C1.2, C3.2, C5.2, C6.2, C9.2, C11.2, C13.2, C14.2, C15.2, C16.2, C17.2, C18.2, C19.2, C20.2, C21.2, C23.2, C24.2, C25.2, C26.1, C27.2, C28.1, C29.2, C30.2, C31.2, C32.2, C34.2, C35.2, C36.2, C37.2, C38.2, C39.2, C40.2, C41.2, C42.2, C43.2, C44.2, FLASH_OPEN8.3, FLASH_OPEN8.4, FLASH_SERV.3, FLASH_SERV.4, GND.1, GND.2, GND.3, GND.4, GND.5, GND.6, IC3.11 (GND), IC4.11 (GND), IC5.11 (GND), IC6.11 (GND), IC7.11 (GND), IC8.11 (GND), IC10.11 (GND), IC11.11 (GND), J4.1, J4.2, J4.3, J4.4, JTAG_OPEN8.4, JTAG_OPEN8.6, JTAG_OPEN8.8, JTAG_OPEN8.10, JTAG_OPEN8.12, JTAG_OPEN8.14, JTAG_OPEN8.16, JTAG_OPEN8.18, JTAG_OPEN8.20, JTAG_SERV.4, JTAG_SERV.6, JTAG_SERV.8, JTAG_SERV.10, JTAG_SERV.12, JTAG_SERV.14, JTAG_SERV.16, JTAG_SERV.18, JTAG_SERV.20, LORA_OPEN8.P$1 (GND_1), LORA_OPEN8.P$8 (GND_2), LORA_OPEN8.P$15 (GND_3), LORA_SERV.P$1 (GND_1), LORA_SERV.P$8 (GND_2), LORA_SERV.P$15 (GND_3), MUX.2, Q1.2 (S), Q2.2 (S), Q3.2 (S), Q4.2 (S), Q5.2 (S), Q16.2 (S), Q17.2 (S), Q18.2 (S), Q19.2 (S), R1.1, R2.1, R4.1, R5.1, R7.1, R8.1, R11.1, R12.1, R13.1, R14.1, R16.1, R17.1, R21.1, R23.1, R26.1, R30.1, R48.1, R53.1, R57.1, R63.1, R65.1, R78.1, R80.1, S1.3 (ON_2), S2.3 (ON_2), S3.3 (ON_2), S4.3 (ON_2), S5.3 (ON_2), S6.3 (ON_2), SPI_OPEN8_2.10, SPI_SERV_1.10, U1.2 (GND), U1.3 (!EN), U2.2 (GND), U2.3 (!EN), U3.2 (GND), U3.3 (!EN), U4.2 (GND), U4.3 (!EN), U5.2 (GND), U5.3 (!EN), U6.2 (GND), U6.3 (!EN), U$1.3, U$1.37, U$2.3, U$2.24, U$2.26, U$2.37, U$3.3, U$3.24, U$3.37, U$4.3, U$4.37, USB-UART_OPEN8_1.1, USB-UART_SERV_1.1
IN_3V3: C3.1, IN_3V3.2, U2.1 (IN)
IN_OPEN8: C6.1, IN_OPEN8.2, U4.1 (IN)
IN_RAM: C9.1, IN_RAM.2, U5.1 (IN)
IN_SERV: C1.1, IN_SERV.2, U1.1 (IN)
IN_VDD: C5.1, IN_VDD.2, U3.1 (IN)
IN_VDDO: C11.1, IN_VDDO.2, U6.1 (IN)
unnamed: R1.2, R3.1, U1.4 (FB)
unnamed: C2.2, R2.2
unnamed: R4.2, R6.1, U5.4 (FB)
unnamed: C10.2, R5.2
unnamed: R11.2, R18.1, U6.4 (FB)
unnamed: R7.2, R10.1, U2.4 (FB)
unnamed: C4.2, R8.2
unnamed: R9.1, R10.2
unnamed: C12.2, R12.2
unnamed: D1.A, R20.1
unnamed: D1.C, Q1.3 (D)
unnamed: R13.2, R19.1, U3.4 (FB)
unnamed: C8.2, R14.2
unnamed: D2.A, R22.1
unnamed: D2.C, Q2.3 (D)
unnamed: IC1.3 (GND), R26.2
unnamed: C25.1, IC1.2 (A), R24.1, Y2.2 (CRYSTAL_2)
unnamed: C26.2, R27.1, Y2.1 (CRYSTAL_1)
unnamed: IC1.5 (VCC), R25.1
unnamed: IC3.3 (A2), OPEN8_LORA.2
unnamed: R32.1, S1.1 (ON_1)
unnamed: R33.1, S2.1 (ON_1)
unnamed: NRESET_OPEN8.2, S1.2 (COM)
unnamed: NRESET_SERV.2, S2.2 (COM)
unnamed: IC3.4 (A3), OPEN8_LORA.4
unnamed: IC3.5 (A4), OPEN8_LORA.6
unnamed: IC3.6 (A5), OPEN8_LORA.8
unnamed: IC4.3 (A2), OPEN8_FLASH.2
unnamed: R15.1, R16.2, U4.4 (FB)
unnamed: IC2.3 (GND), R30.2
unnamed: C7.2, R17.2
unnamed: C27.1, IC2.2 (A), R28.1, Y3.2 (CRYSTAL_2)
unnamed: C28.2, R31.1, Y3.1 (CRYSTAL_1)
unnamed: IC4.4 (A3), OPEN8_FLASH.4
unnamed: IC2.5 (VCC), R29.1
unnamed: IC4.5 (A4), OPEN8_FLASH.6
unnamed: IC4.6 (A5), OPEN8_FLASH.8
unnamed: IC11.4 (A3), OPEN8_SPI.2
unnamed: IC11.5 (A4), OPEN8_SPI.4
unnamed: IC11.6 (A5), OPEN8_SPI.6
unnamed: IC11.7 (A6), OPEN8_SPI.8
unnamed: R41.1, S4.1 (ON_1)
unnamed: D4.A, R40.1
unnamed: D4.C, Q3.3 (D)
unnamed: OPEN8_SW.4, S4.2 (COM)
unnamed: R39.1, S3.1 (ON_1)
unnamed: OPEN8_SW.2, S3.2 (COM)
unnamed: IC6.1 (A1), OPEN8_JTAG.2
unnamed: IC6.3 (A2), OPEN8_JTAG.4
unnamed: IC6.4 (A3), OPEN8_JTAG.6
unnamed: IC6.5 (A4), OPEN8_JTAG.8
unnamed: IC6.6 (A5), OPEN8_JTAG.10
unnamed: IC6.7 (A6), OPEN8_UART.2
unnamed: IC6.8 (A7), OPEN8_UART.4
unnamed: IC5.3 (A2), SERV_LORA.2
unnamed: IC5.4 (A3), SERV_LORA.4
unnamed: D19.A, R62.1
unnamed: IC5.5 (A4), SERV_LORA.6
unnamed: IC5.6 (A5), SERV_LORA.8
unnamed: IC7.3 (A2), SERV_FLASH.2
unnamed: IC7.4 (A3), SERV_FLASH.4
unnamed: IC7.5 (A4), SERV_FLASH.6
unnamed: IC7.6 (A5), SERV_FLASH.8
unnamed: D19.C, Q16.3 (D)
unnamed: D20.A, R64.1
unnamed: D20.C, Q17.3 (D)
unnamed: D21.A, R77.1
unnamed: D21.C, Q18.3 (D)
unnamed: D22.A, R79.1
unnamed: D22.C, Q19.3 (D)
unnamed: IC8.3 (A2), SERV_SPI.2
unnamed: IC8.4 (A3), SERV_SPI.4
unnamed: IC8.5 (A4), SERV_SPI.6
unnamed: IC8.6 (A5), SERV_SPI.8
unnamed: IC10.1 (A1), SERV_JTAG.2
unnamed: IC10.3 (A2), SERV_JTAG.4
unnamed: IC10.4 (A3), SERV_JTAG.6
unnamed: IC10.5 (A4), SERV_JTAG.8
unnamed: IC10.6 (A5), SERV_JTAG.10
unnamed: IC10.7 (A6), SERV_UART.2
unnamed: IC10.8 (A7), SERV_UART.4
unnamed: D3.A, R52.1
unnamed: D3.C, Q4.3 (D)
unnamed: R54.1, S5.1 (ON_1)
unnamed: S5.2 (COM), SERV_SW.2
unnamed: R55.1, S6.1 (ON_1)
unnamed: S6.2 (COM), SERV_SW.4
unnamed: D5.A, R56.1
unnamed: D5.C, Q5.3 (D)
OPEN8_FLASH_CIPO: FLASH_OPEN8.8, IC4.18 (B2)
OPEN8_FLASH_COPI: FLASH_OPEN8.10, IC4.16 (B4)
OPEN8_FLASH_CS: FLASH_OPEN8.12, IC4.17 (B3)
OPEN8_FLASH_SCK: FLASH_OPEN8.6, IC4.15 (B5)
OPEN8_JTAG_TCK: IC6.16 (B4), JTAG_OPEN8.9
OPEN8_JTAG_TDI: IC6.20 (B1), JTAG_OPEN8.5
OPEN8_JTAG_TDO: IC6.18 (B2), JTAG_OPEN8.13
OPEN8_JTAG_TMS: IC6.15 (B5), JTAG_OPEN8.7
OPEN8_JTAG_TRST: IC6.17 (B3), JTAG_OPEN8.3
OPEN8_LED: OPEN8_LED.2, Q3.1 (G), R48.2
OPEN8_LORA_CS: IC3.17 (B3), LORA_OPEN8.P$5 (NSS)
OPEN8_LORA_MISO: IC3.15 (B5), LORA_OPEN8.P$2 (MISO)
OPEN8_LORA_MOSI: IC3.16 (B4), LORA_OPEN8.P$3 (MOSI)
OPEN8_LORA_SCK: IC3.18 (B2), LORA_OPEN8.P$4 (SCK)
OPEN8_PROG_CS: IC11.16 (B4), SPI_OPEN8_2.4
OPEN8_PROG_MISO: IC11.14 (B6), SPI_OPEN8_2.3
OPEN8_PROG_MOSI: IC11.15 (B5), SPI_OPEN8_2.2
OPEN8_PROG_SCK: IC11.17 (B3), SPI_OPEN8_2.1
OPEN8_UART_RX: IC6.13 (B7), USB-UART_OPEN8_1.2
OPEN8_UART_TX: IC6.14 (B6), USB-UART_OPEN8_1.4
OUT_3V3: C4.1, POWER.1, R9.2, U2.5 (OUT)
OUT_OPEN8: C7.1, POWER.7, R15.2, U4.5 (OUT)
OUT_RAM: C10.1, POWER.11, R6.2, U5.5 (OUT)
OUT_SERV: C2.1, POWER.9, R3.2, U1.5 (OUT)
OUT_VDD: C8.1, POWER.5, R19.2, U3.5 (OUT)
OUT_VDDO: C12.1, POWER.3, R18.2, U6.5 (OUT)
SERV_FLASH_CIPO: FLASH_SERV.8, IC7.18 (B2)
SERV_FLASH_COPI: FLASH_SERV.10, IC7.16 (B4)
SERV_FLASH_CS: FLASH_SERV.12, IC7.17 (B3)
SERV_FLASH_SCK: FLASH_SERV.6, IC7.15 (B5)
SERV_JTAG_TCK: IC10.16 (B4), JTAG_SERV.9
SERV_JTAG_TDI: IC10.17 (B3), JTAG_SERV.5
SERV_JTAG_TDO: IC10.18 (B2), JTAG_SERV.13
SERV_JTAG_TMS: IC10.15 (B5), JTAG_SERV.7
SERV_JTAG_TRST: IC10.20 (B1), JTAG_SERV.3
SERV_LED: Q4.1 (G), R53.2, SERV_LED.2
SERV_LORA_CS: IC5.17 (B3), LORA_SERV.P$5 (NSS)
SERV_LORA_MISO: IC5.15 (B5), LORA_SERV.P$2 (MISO)
SERV_LORA_MOSI: IC5.16 (B4), LORA_SERV.P$3 (MOSI)
SERV_LORA_SCK: IC5.18 (B2), LORA_SERV.P$4 (SCK)
SERV_PROG_CS: IC8.17 (B3), SPI_SERV_1.4
SERV_PROG_MISO: IC8.15 (B5), SPI_SERV_1.3
SERV_PROG_MOSI: IC8.16 (B4), SPI_SERV_1.2
SERV_PROG_SCK: IC8.18 (B2), SPI_SERV_1.1
SERV_UART_RX: IC10.14 (B6), USB-UART_SERV_1.2
SERV_UART_TX: IC10.13 (B7), USB-UART_SERV_1.4
SMA_CLK: CLOCK.5, J4.5
VDD: C19.1, C20.1, POWER.6, Q1.1 (G), R21.2, U$1.13, U$2.13, U$3.15, U$4.13
VDDO: C16.1, C17.1, C30.1, C32.1, C34.1, C35.1, C38.1, C40.1, C42.1, C43.1, IC3.2 (VCCA), IC3.10 (OE), IC4.2 (VCCA), IC4.10 (OE), IC5.2 (VCCA), IC5.10 (OE), IC6.2 (VCCA), IC6.10 (OE), IC7.2 (VCCA), IC7.10 (OE), IC8.2 (VCCA), IC8.10 (OE), IC10.2 (VCCA), IC10.10 (OE), IC11.2 (VCCA), IC11.10 (OE), POWER.4, Q19.1 (G), R80.2, U$1.27, U$2.25, U$3.25, U$4.27
VDD_3V3: C21.1, C29.1, C31.1, C36.1, C37.1, C39.1, C41.1, C44.1, FLASH_OPEN8.1, FLASH_OPEN8.2, FLASH_SERV.1, FLASH_SERV.2, IC3.19 (VCCB), IC4.19 (VCCB), IC5.19 (VCCB), IC6.19 (VCCB), IC7.19 (VCCB), IC8.19 (VCCB), IC10.19 (VCCB), IC11.19 (VCCB), JTAG_OPEN8.1, JTAG_OPEN8.2, JTAG_SERV.1, JTAG_SERV.2, LORA_OPEN8.P$12 (3.3V), LORA_SERV.P$12 (3.3V), POWER.2, Q18.1 (G), R20.2, R22.2, R25.2, R29.2, R32.2, R33.2, R34.1, R39.2, R40.2, R41.2, R52.2, R54.2, R55.2, R56.2, R62.2, R64.2, R77.2, R78.2, R79.2, USB-UART_OPEN8_1.3, USB-UART_SERV_1.3
VDD_5V: IN_3V3.1, IN_OPEN8.1, IN_RAM.1, IN_SERV.1, IN_VDD.1, IN_VDDO.1, Q5.1 (G), R57.2, USB-UART_OPEN8_2.2, USB-UART_SERV_2.2

Notes on the sheet:
POWER
CLOCK GENERATOR
RESET
Mounting holes
Pin Connection
OPEN8_LORA
SERV_LORA
OPEN8_FLASH
OPEN8_SPI
OPEN8_JTAG
OPEN8_SWITCH
MUX
OPEN8_LED
32KHZ
8MHZ
SMA
SERV_LED
SERV_SWITCH
SERV_JTAG
SERV_UART
SERV_SPI
SERV_FLASH

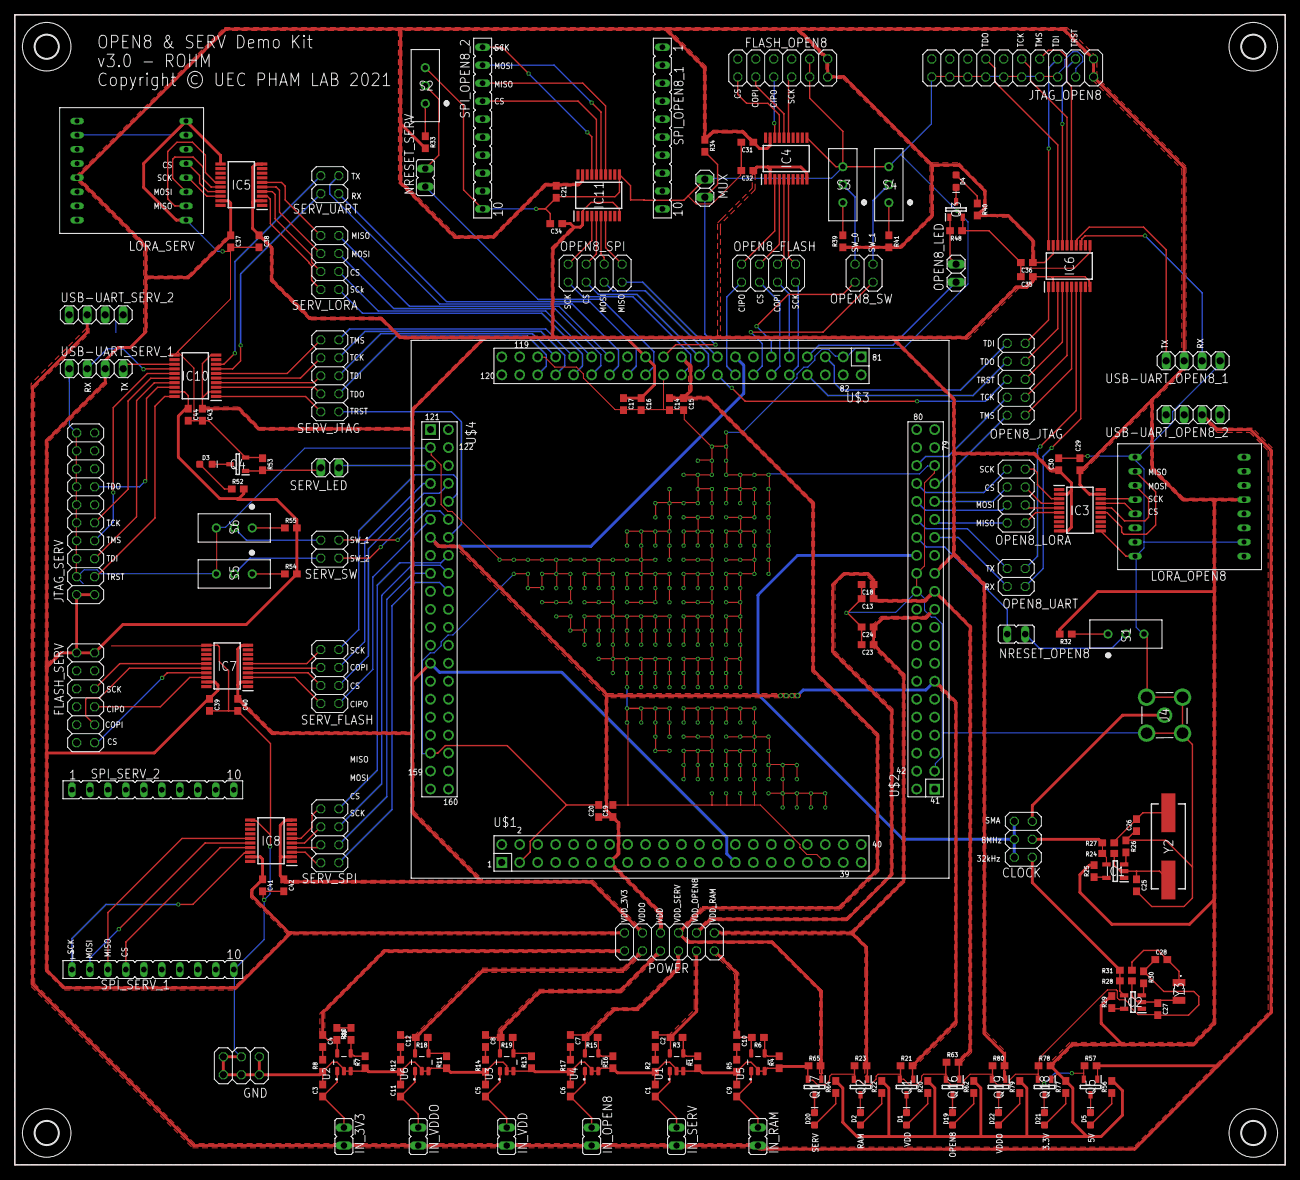
[picture p79: board serv_open8_rohm.brd from above]

Board: 2 copper layers, 179.5 x 162.5 mm, 185 parts (0 on the bottom side), 200 nets.
