Khaiduy/Open8_PCB/QFP160_new_socket/qfp160_socket_new.brd

## EAGLE design QFP160_new_socket/qfp160_socket_new.brd (2021-11-01)

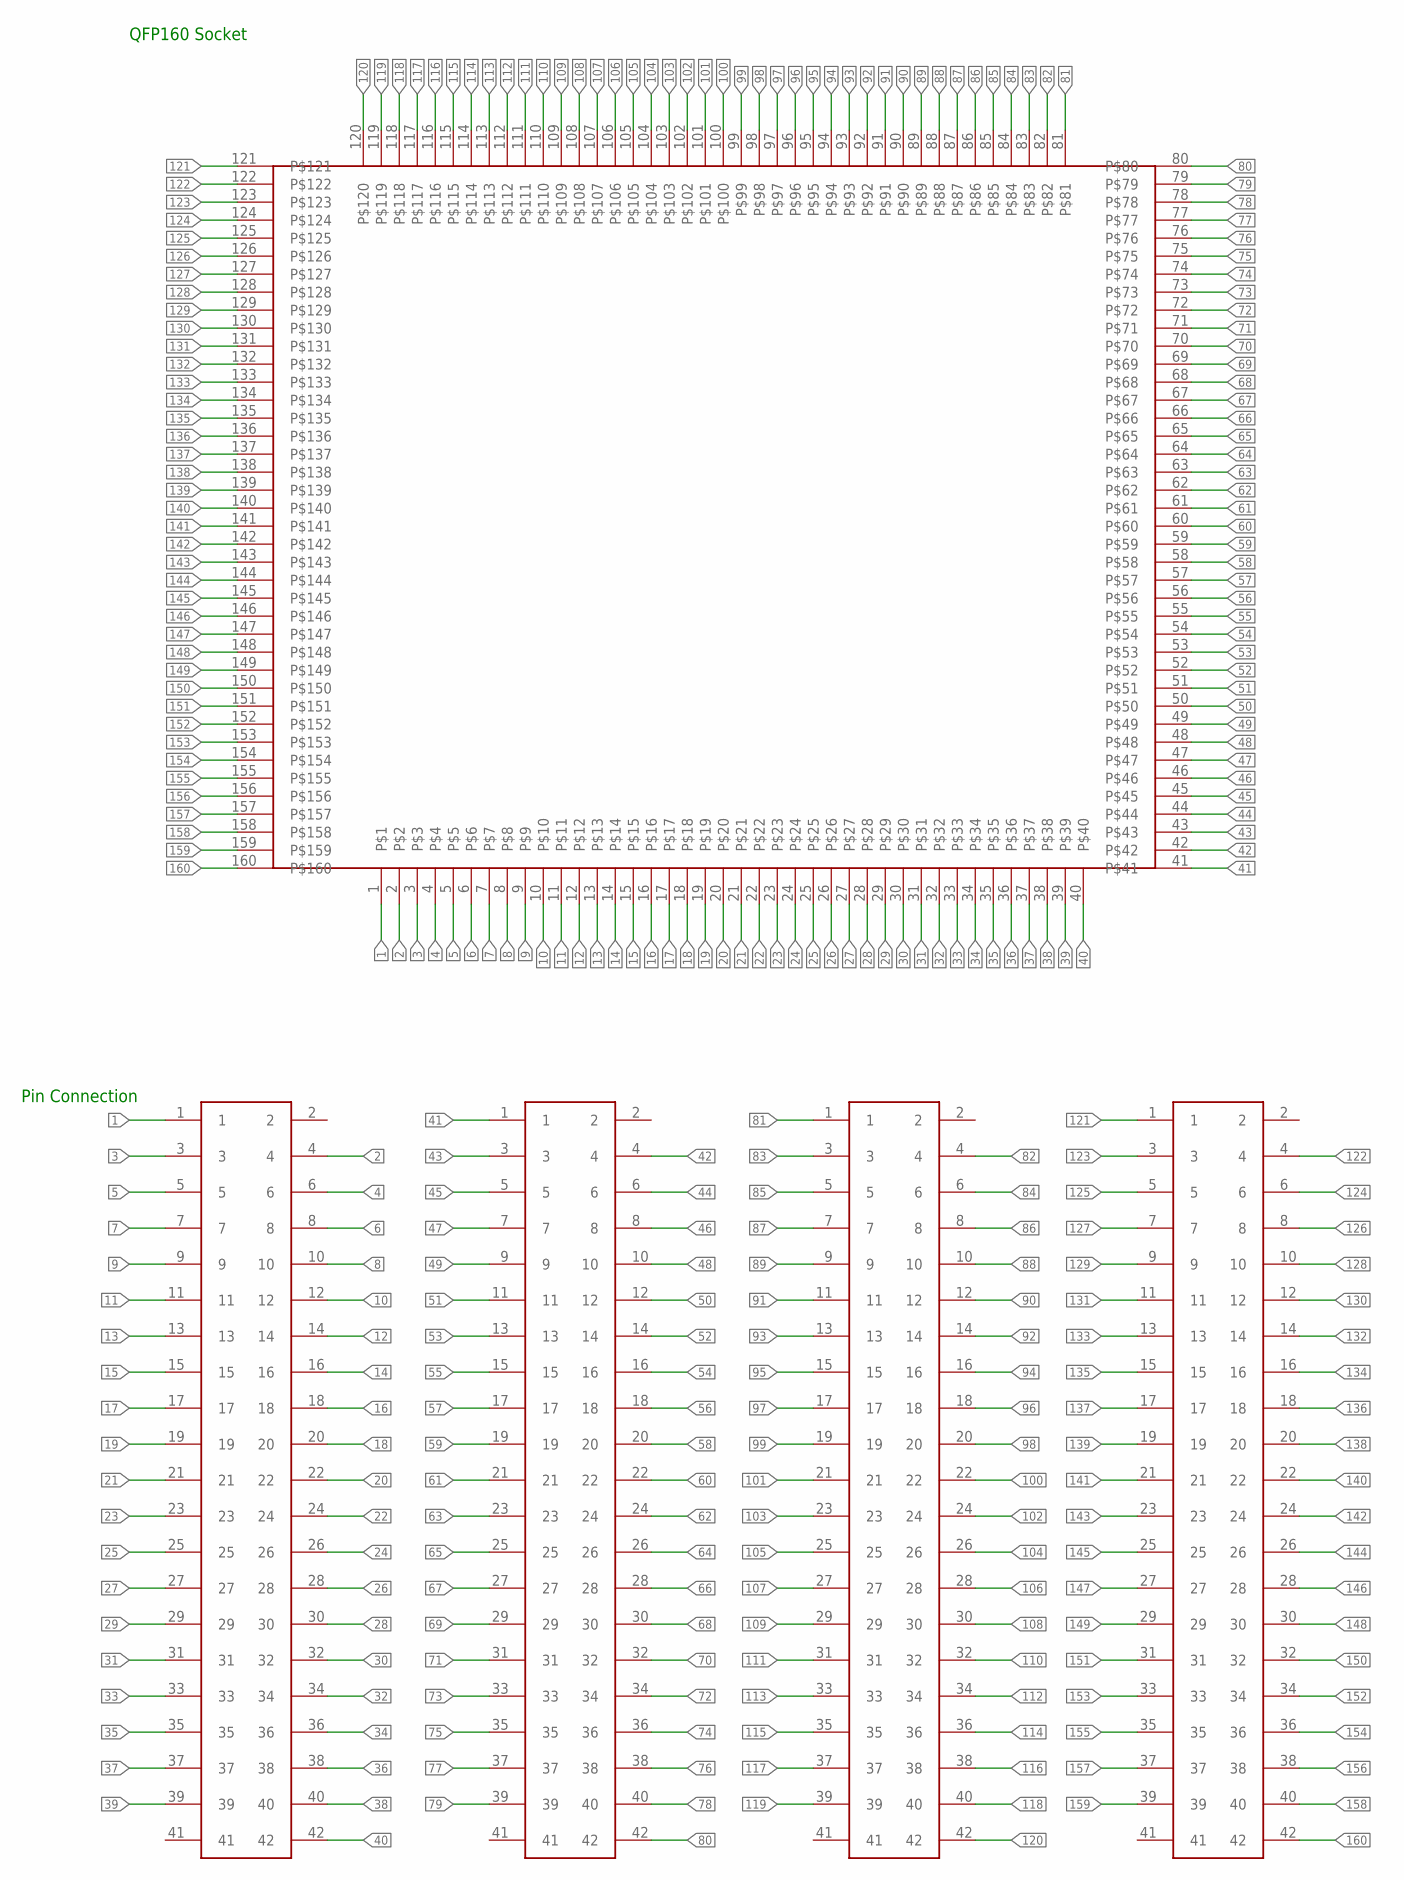
[picture p80: schematic qfp160_socket_new.sch]

Parts:
U$1, U$2, U$3, U$4: 2X41_HEADER
U$5: QFP160_SOCKET

Connections:
1: U$1.1, U$5.1
2: U$1.4, U$5.2
3: U$1.3, U$5.3
4: U$1.6, U$5.4
5: U$1.5, U$5.5
6: U$1.8, U$5.6
7: U$1.7, U$5.7
8: U$1.10, U$5.8
9: U$1.9, U$5.9
10: U$1.12, U$5.10
11: U$1.11, U$5.11
12: U$1.14, U$5.12
13: U$1.13, U$5.13
14: U$1.16, U$5.14
15: U$1.15, U$5.15
16: U$1.18, U$5.16
17: U$1.17, U$5.17
18: U$1.20, U$5.18
19: U$1.19, U$5.19
20: U$1.22, U$5.20
21: U$1.21, U$5.21
22: U$1.24, U$5.22
23: U$1.23, U$5.23
24: U$1.26, U$5.24
25: U$1.25, U$5.25
26: U$1.28, U$5.26
27: U$1.27, U$5.27
28: U$1.30, U$5.28
29: U$1.29, U$5.29
30: U$1.32, U$5.30
31: U$1.31, U$5.31
32: U$1.34, U$5.32
33: U$1.33, U$5.33
34: U$1.36, U$5.34
35: U$1.35, U$5.35
36: U$1.38, U$5.36
37: U$1.37, U$5.37
38: U$1.40, U$5.38
39: U$1.39, U$5.39
40: U$1.42, U$5.40
41: U$2.1, U$5.41
42: U$2.4, U$5.42
43: U$2.3, U$5.43
44: U$2.6, U$5.44
45: U$2.5, U$5.45
46: U$2.8, U$5.46
47: U$2.7, U$5.47
48: U$2.10, U$5.48
49: U$2.9, U$5.49
50: U$2.12, U$5.50
51: U$2.11, U$5.51
52: U$2.14, U$5.52
53: U$2.13, U$5.53
54: U$2.16, U$5.54
55: U$2.15, U$5.55
56: U$2.18, U$5.56
57: U$2.17, U$5.57
58: U$2.20, U$5.58
59: U$2.19, U$5.59
60: U$2.22, U$5.60
61: U$2.21, U$5.61
62: U$2.24, U$5.62
63: U$2.23, U$5.63
64: U$2.26, U$5.64
65: U$2.25, U$5.65
66: U$2.28, U$5.66
67: U$2.27, U$5.67
68: U$2.30, U$5.68
69: U$2.29, U$5.69
70: U$2.32, U$5.70
71: U$2.31, U$5.71
72: U$2.34, U$5.72
73: U$2.33, U$5.73
74: U$2.36, U$5.74
75: U$2.35, U$5.75
76: U$2.38, U$5.76
77: U$2.37, U$5.77
78: U$2.40, U$5.78
79: U$2.39, U$5.79
80: U$2.42, U$5.80
81: U$3.1, U$5.81
82: U$3.4, U$5.82
83: U$3.3, U$5.83
84: U$3.6, U$5.84
85: U$3.5, U$5.85
86: U$3.8, U$5.86
87: U$3.7, U$5.87
88: U$3.10, U$5.88
89: U$3.9, U$5.89
90: U$3.12, U$5.90
91: U$3.11, U$5.91
92: U$3.14, U$5.92
93: U$3.13, U$5.93
94: U$3.16, U$5.94
95: U$3.15, U$5.95
96: U$3.18, U$5.96
97: U$3.17, U$5.97
98: U$3.20, U$5.98
99: U$3.19, U$5.99
100: U$3.22, U$5.100
101: U$3.21, U$5.101
102: U$3.24, U$5.102
103: U$3.23, U$5.103
104: U$3.26, U$5.104
105: U$3.25, U$5.105
106: U$3.28, U$5.106
107: U$3.27, U$5.107
108: U$3.30, U$5.108
109: U$3.29, U$5.109
110: U$3.32, U$5.110
111: U$3.31, U$5.111
112: U$3.34, U$5.112
113: U$3.33, U$5.113
114: U$3.36, U$5.114
115: U$3.35, U$5.115
116: U$3.38, U$5.116
117: U$3.37, U$5.117
118: U$3.40, U$5.118
119: U$3.39, U$5.119
120: U$3.42, U$5.120
121: U$4.1, U$5.121
122: U$4.4, U$5.122
123: U$4.3, U$5.123
124: U$4.6, U$5.124
125: U$4.5, U$5.125
126: U$4.8, U$5.126
127: U$4.7, U$5.127
128: U$4.10, U$5.128
129: U$4.9, U$5.129
130: U$4.12, U$5.130
131: U$4.11, U$5.131
132: U$4.14, U$5.132
133: U$4.13, U$5.133
134: U$4.16, U$5.134
135: U$4.15, U$5.135
136: U$4.18, U$5.136
137: U$4.17, U$5.137
138: U$4.20, U$5.138
139: U$4.19, U$5.139
140: U$4.22, U$5.140
141: U$4.21, U$5.141
142: U$4.24, U$5.142
143: U$4.23, U$5.143
144: U$4.26, U$5.144
145: U$4.25, U$5.145
146: U$4.28, U$5.146
147: U$4.27, U$5.147
148: U$4.30, U$5.148
149: U$4.29, U$5.149
150: U$4.32, U$5.150
151: U$4.31, U$5.151
152: U$4.34, U$5.152
153: U$4.33, U$5.153
154: U$4.36, U$5.154
155: U$4.35, U$5.155
156: U$4.38, U$5.156
157: U$4.37, U$5.157
158: U$4.40, U$5.158
159: U$4.39, U$5.159
160: U$4.42, U$5.160

Notes on the sheet:
QFP160 Socket
Pin Connection
