Khaiduy/Open8_PCB/QFP160_new_socket/qfp160_socket_new.brd

## EAGLE design QFP160_new_socket/qfp160_socket_new.brd (continued)

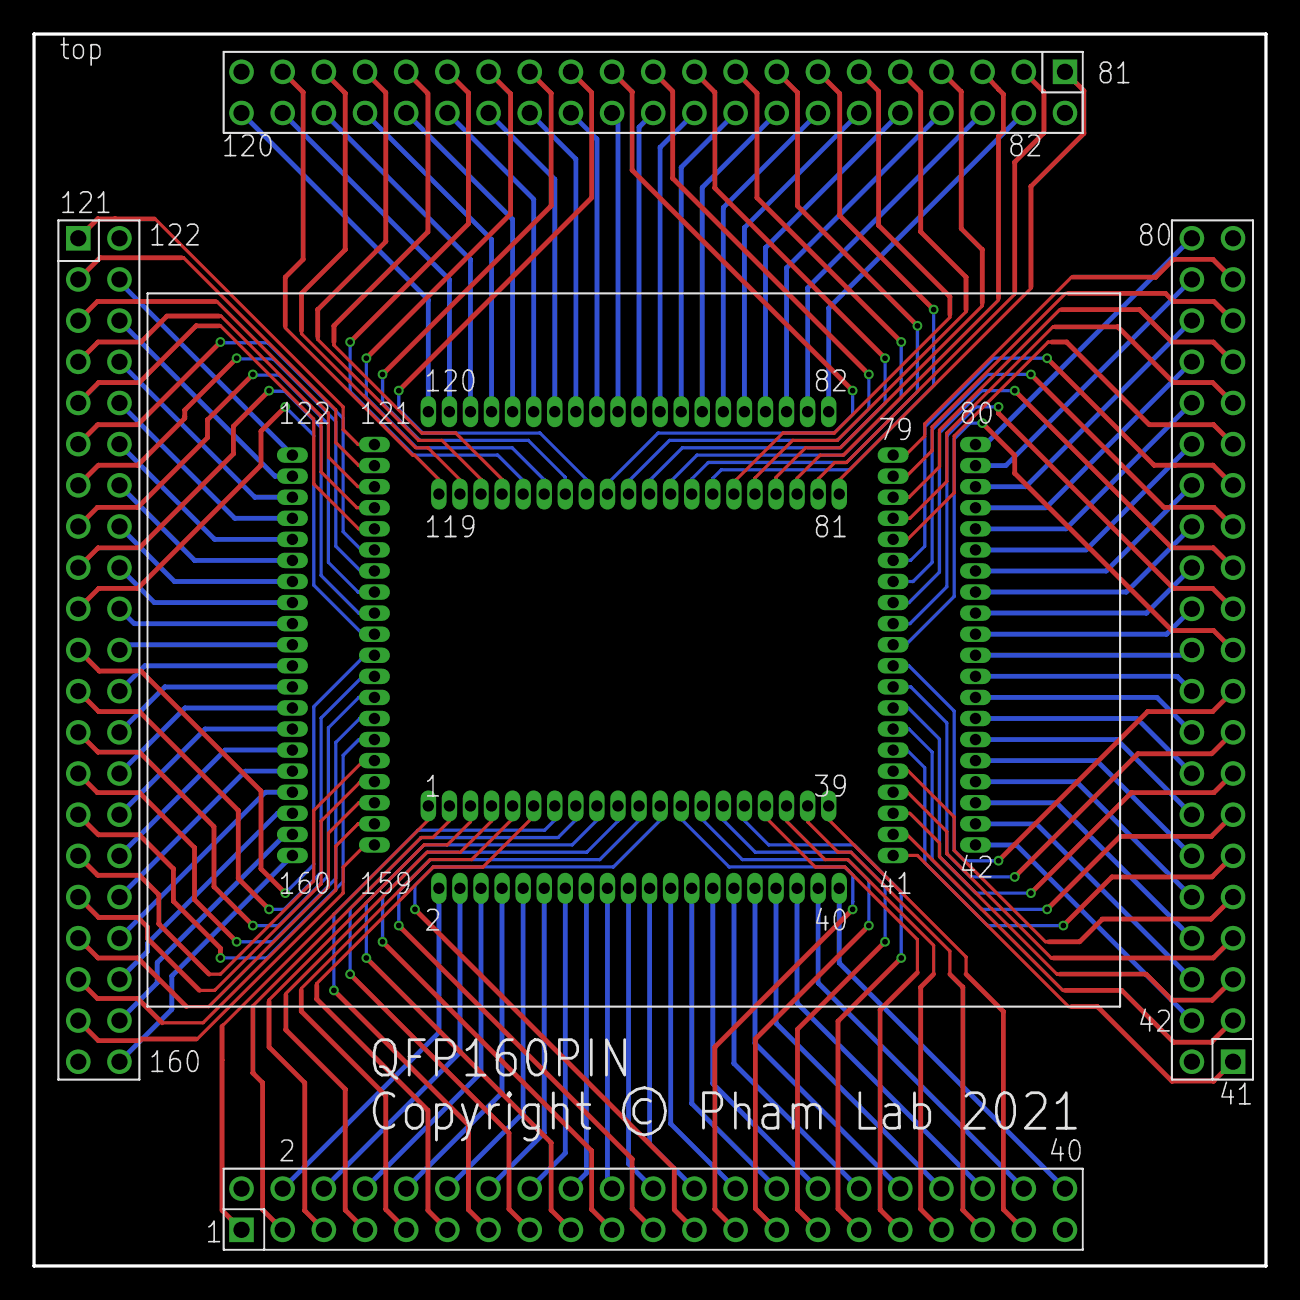
[picture p81: board qfp160_socket_new.brd from above]

Board: 2 copper layers, 76.0 x 76.0 mm, 5 parts (0 on the bottom side), 160 nets.
