Khaiduy/Open8_PCB/TR4_PGA257(v4.0)/TR4.brd

## EAGLE design TR4_PGA257(v4.0)/TR4.brd (continued)

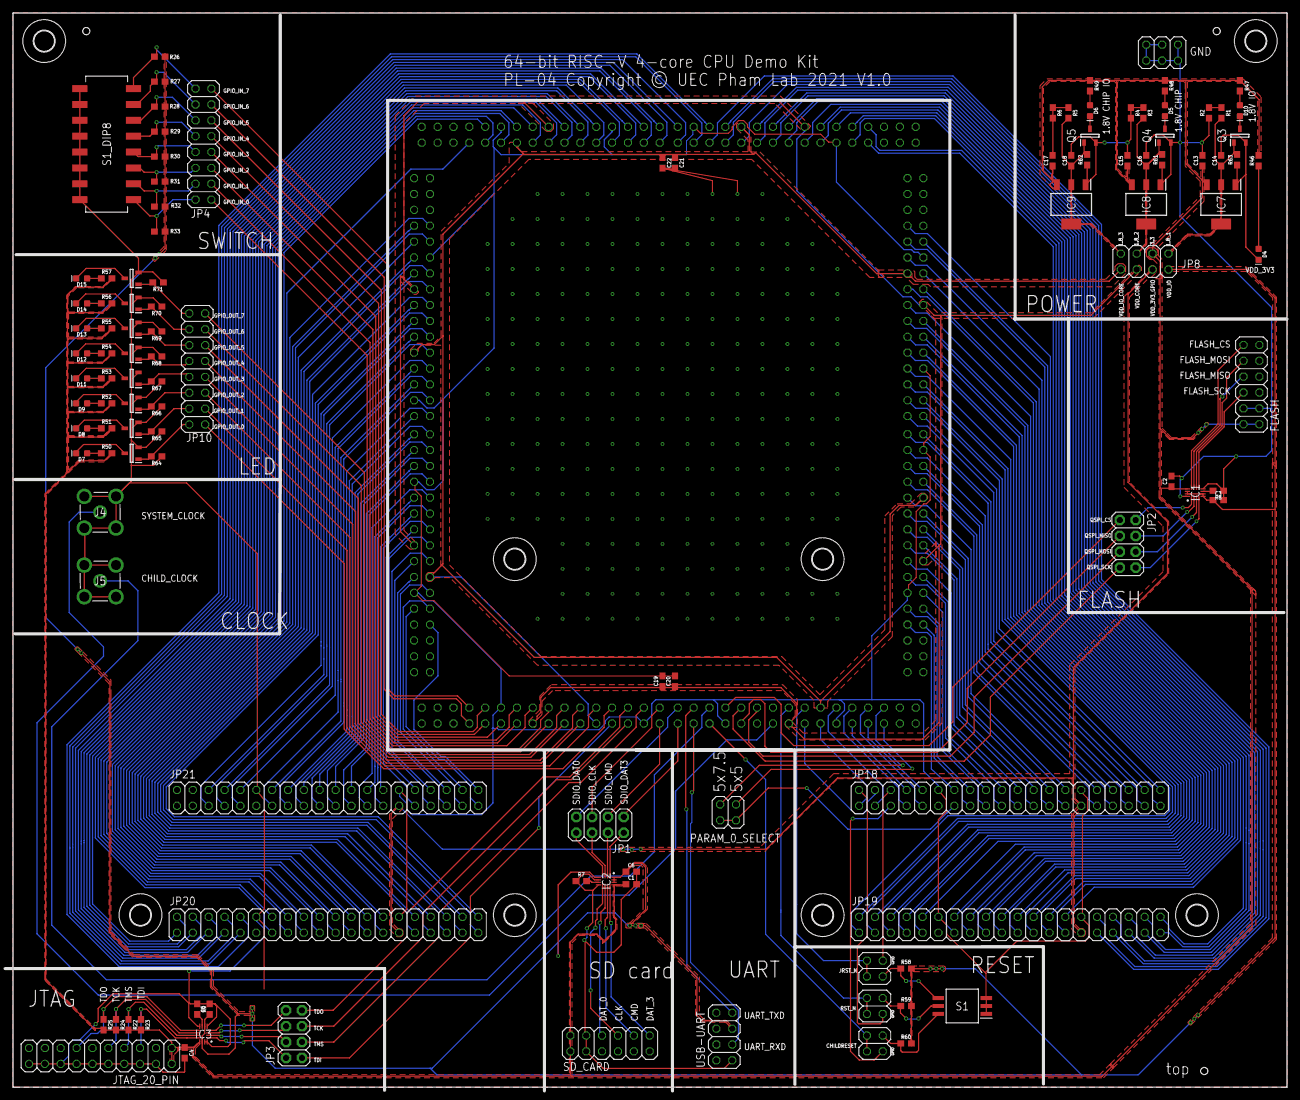
[picture p88: board TR4.brd from above]

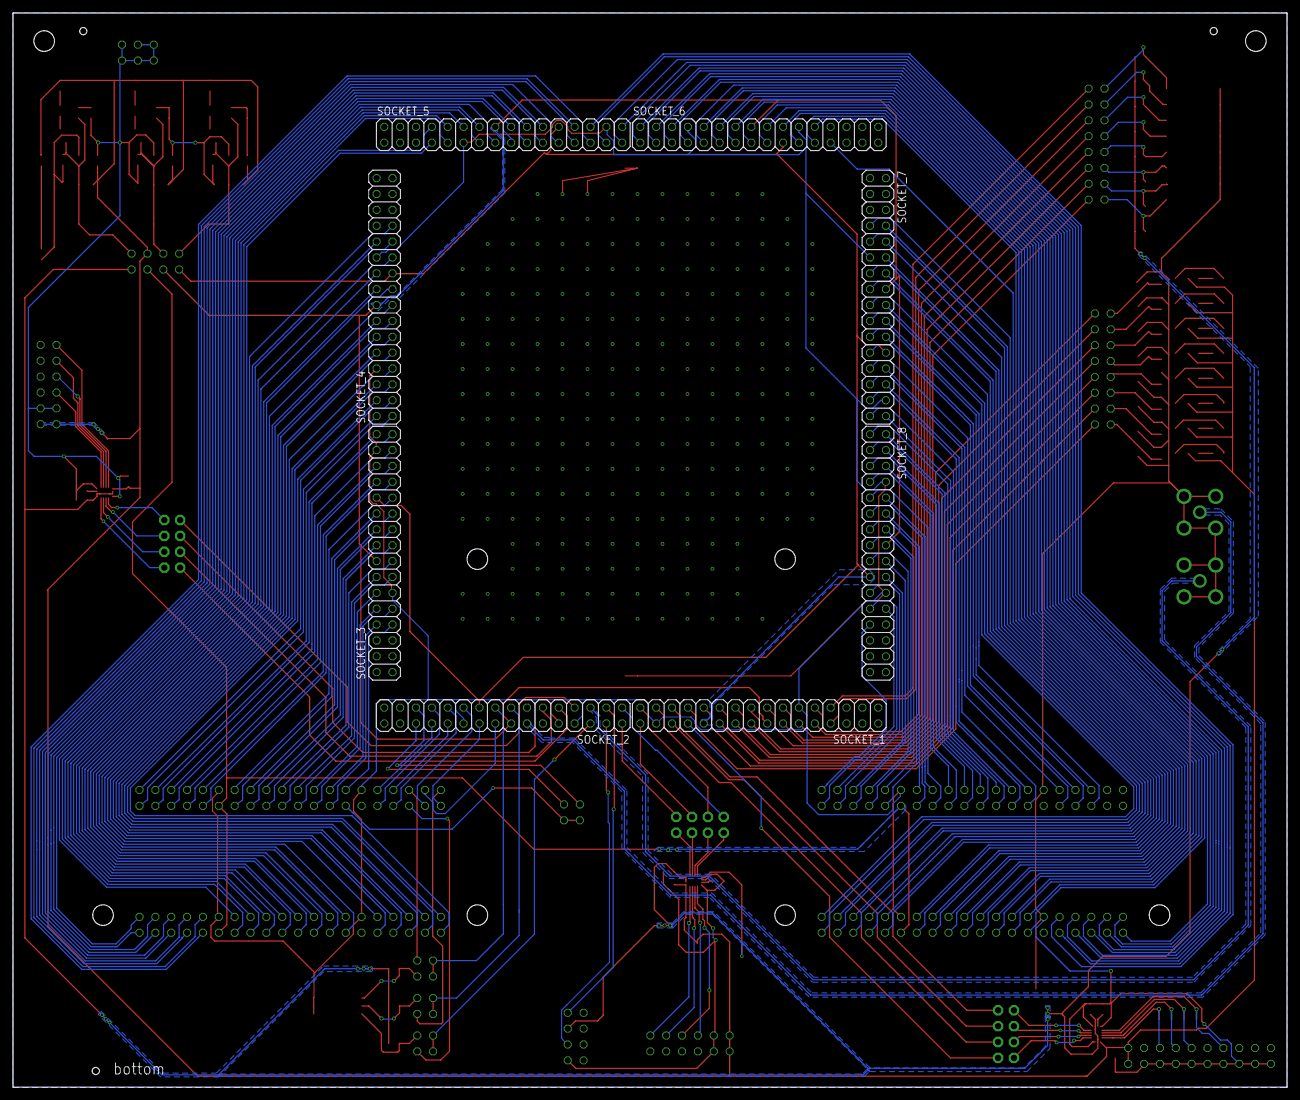
[picture p89: board TR4.brd from below]

Board: 2 copper layers, 204.0 x 172.0 mm, 131 parts (8 on the bottom side), 255 nets.
