Khaiduy/Open8_PCB/TR4_PGA257(v4.0)/PGA257_socket.brd

## EAGLE design TR4_PGA257(v4.0)/PGA257_socket.brd (2021-08-17)

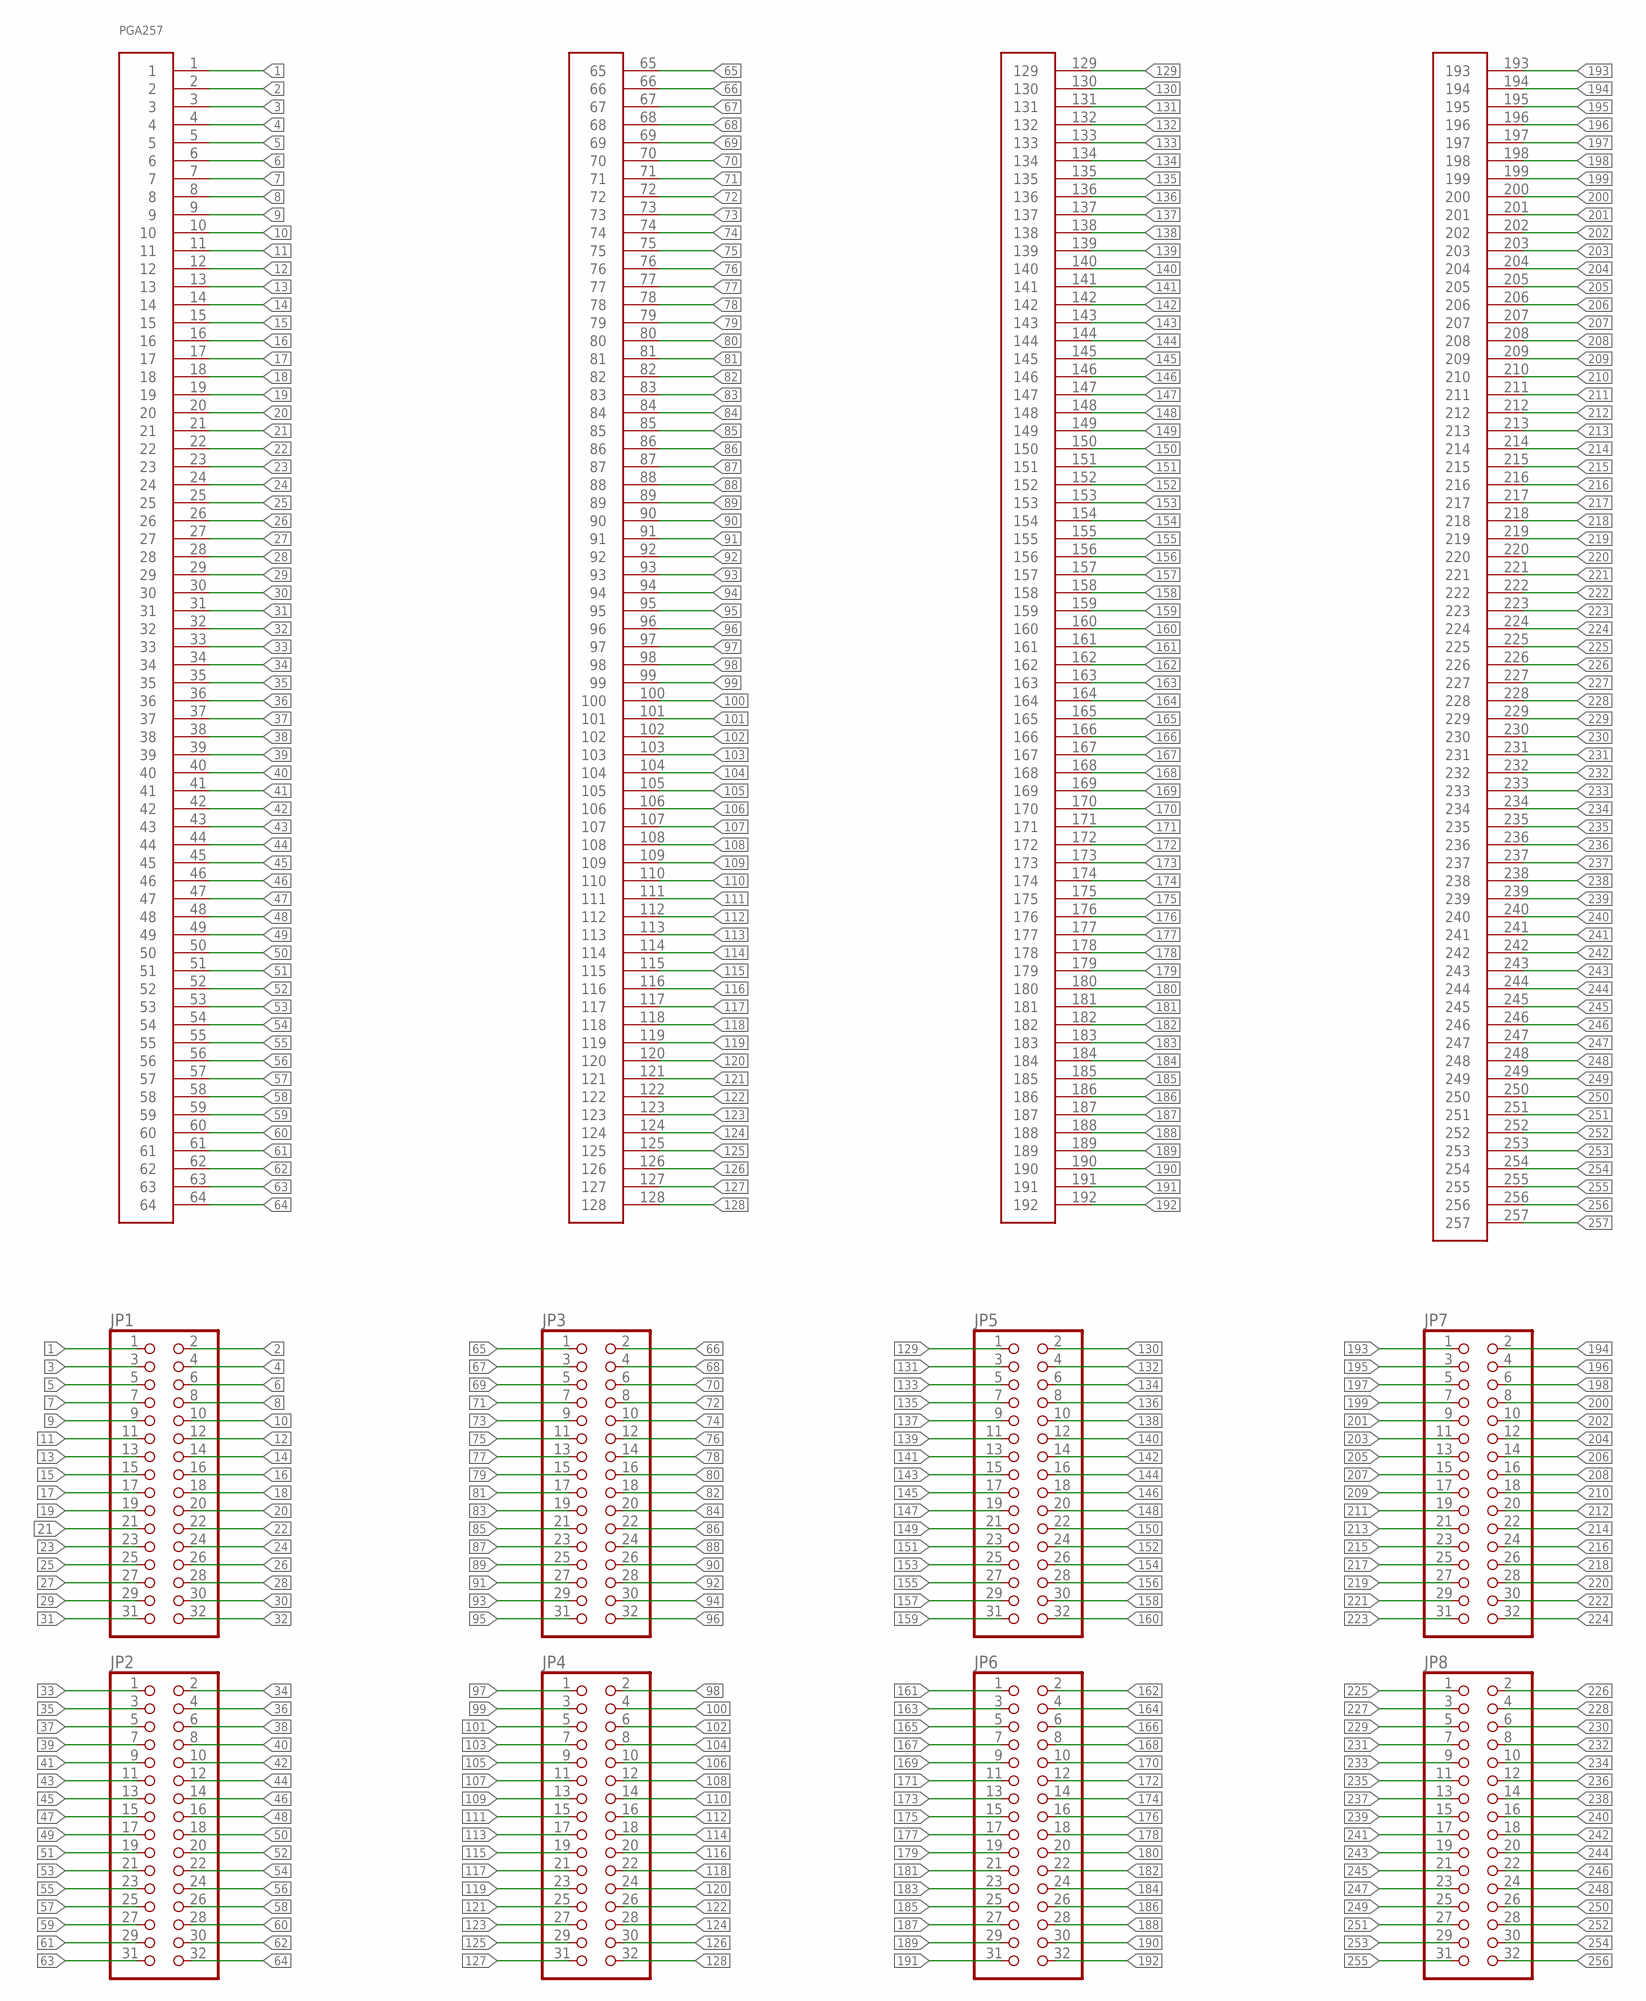
[picture p90: schematic PGA257_socket.sch]

Parts:
JP1, JP2, JP3, JP4, JP5, JP6, JP7, JP8: PINHD-2X16; 2X16
PGA257: PGA257

Connections:
1: JP1.1, PGA257.1
2: JP1.2, PGA257.2
3: JP1.3, PGA257.3
4: JP1.4, PGA257.4
5: JP1.5, PGA257.5
6: JP1.6, PGA257.6
7: JP1.7, PGA257.7
8: JP1.8, PGA257.8
9: JP1.9, PGA257.9
10: JP1.10, PGA257.10
11: JP1.11, PGA257.11
12: JP1.12, PGA257.12
13: JP1.13, PGA257.13
14: JP1.14, PGA257.14
15: JP1.15, PGA257.15
16: JP1.16, PGA257.16
17: JP1.17, PGA257.17
18: JP1.18, PGA257.18
19: JP1.19, PGA257.19
20: JP1.20, PGA257.20
21: JP1.21, PGA257.21
22: JP1.22, PGA257.22
23: JP1.23, PGA257.23
24: JP1.24, PGA257.24
25: JP1.25, PGA257.25
26: JP1.26, PGA257.26
27: JP1.27, PGA257.27
28: JP1.28, PGA257.28
29: JP1.29, PGA257.29
30: JP1.30, PGA257.30
31: JP1.31, PGA257.31
32: JP1.32, PGA257.32
33: JP2.1, PGA257.33
34: JP2.2, PGA257.34
35: JP2.3, PGA257.35
36: JP2.4, PGA257.36
37: JP2.5, PGA257.37
38: JP2.6, PGA257.38
39: JP2.7, PGA257.39
40: JP2.8, PGA257.40
41: JP2.9, PGA257.41
42: JP2.10, PGA257.42
43: JP2.11, PGA257.43
44: JP2.12, PGA257.44
45: JP2.13, PGA257.45
46: JP2.14, PGA257.46
47: JP2.15, PGA257.47
48: JP2.16, PGA257.48
49: JP2.17, PGA257.49
50: JP2.18, PGA257.50
51: JP2.19, PGA257.51
52: JP2.20, PGA257.52
53: JP2.21, PGA257.53
54: JP2.22, PGA257.54
55: JP2.23, PGA257.55
56: JP2.24, PGA257.56
57: JP2.25, PGA257.57
58: JP2.26, PGA257.58
59: JP2.27, PGA257.59
60: JP2.28, PGA257.60
61: JP2.29, PGA257.61
62: JP2.30, PGA257.62
63: JP2.31, PGA257.63
64: JP2.32, PGA257.64
65: JP3.1, PGA257.65
66: JP3.2, PGA257.66
67: JP3.3, PGA257.67
68: JP3.4, PGA257.68
69: JP3.5, PGA257.69
70: JP3.6, PGA257.70
71: JP3.7, PGA257.71
72: JP3.8, PGA257.72
73: JP3.9, PGA257.73
74: JP3.10, PGA257.74
75: JP3.11, PGA257.75
76: JP3.12, PGA257.76
77: JP3.13, PGA257.77
78: JP3.14, PGA257.78
79: JP3.15, PGA257.79
80: JP3.16, PGA257.80
81: JP3.17, PGA257.81
82: JP3.18, PGA257.82
83: JP3.19, PGA257.83
84: JP3.20, PGA257.84
85: JP3.21, PGA257.85
86: JP3.22, PGA257.86
87: JP3.23, PGA257.87
88: JP3.24, PGA257.88
89: JP3.25, PGA257.89
90: JP3.26, PGA257.90
91: JP3.27, PGA257.91
92: JP3.28, PGA257.92
93: JP3.29, PGA257.93
94: JP3.30, PGA257.94
95: JP3.31, PGA257.95
96: JP3.32, PGA257.96
97: JP4.1, PGA257.97
98: JP4.2, PGA257.98
99: JP4.3, PGA257.99
100: JP4.4, PGA257.100
101: JP4.5, PGA257.101
102: JP4.6, PGA257.102
103: JP4.7, PGA257.103
104: JP4.8, PGA257.104
105: JP4.9, PGA257.105
106: JP4.10, PGA257.106
107: JP4.11, PGA257.107
108: JP4.12, PGA257.108
109: JP4.13, PGA257.109
110: JP4.14, PGA257.110
111: JP4.15, PGA257.111
112: JP4.16, PGA257.112
113: JP4.17, PGA257.113
114: JP4.18, PGA257.114
115: JP4.19, PGA257.115
116: JP4.20, PGA257.116
117: JP4.21, PGA257.117
118: JP4.22, PGA257.118
119: JP4.23, PGA257.119
120: JP4.24, PGA257.120
121: JP4.25, PGA257.121
122: JP4.26, PGA257.122
123: JP4.27, PGA257.123
124: JP4.28, PGA257.124
125: JP4.29, PGA257.125
126: JP4.30, PGA257.126
127: JP4.31, PGA257.127
128: JP4.32, PGA257.128
129: JP5.1, PGA257.129
130: JP5.2, PGA257.130
131: JP5.3, PGA257.131
132: JP5.4, PGA257.132
133: JP5.5, PGA257.133
134: JP5.6, PGA257.134
135: JP5.7, PGA257.135
136: JP5.8, PGA257.136
137: JP5.9, PGA257.137
138: JP5.10, PGA257.138
139: JP5.11, PGA257.139
140: JP5.12, PGA257.140
141: JP5.13, PGA257.141
142: JP5.14, PGA257.142
143: JP5.15, PGA257.143
144: JP5.16, PGA257.144
145: JP5.17, PGA257.145
146: JP5.18, PGA257.146
147: JP5.19, PGA257.147
148: JP5.20, PGA257.148
149: JP5.21, PGA257.149
150: JP5.22, PGA257.150
151: JP5.23, PGA257.151
152: JP5.24, PGA257.152
153: JP5.25, PGA257.153
154: JP5.26, PGA257.154
155: JP5.27, PGA257.155
156: JP5.28, PGA257.156
157: JP5.29, PGA257.157
158: JP5.30, PGA257.158
159: JP5.31, PGA257.159
160: JP5.32, PGA257.160
161: JP6.1, PGA257.161
162: JP6.2, PGA257.162
163: JP6.3, PGA257.163
164: JP6.4, PGA257.164
165: JP6.5, PGA257.165
166: JP6.6, PGA257.166
167: JP6.7, PGA257.167
168: JP6.8, PGA257.168
169: JP6.9, PGA257.169
170: JP6.10, PGA257.170
171: JP6.11, PGA257.171
172: JP6.12, PGA257.172
173: JP6.13, PGA257.173
174: JP6.14, PGA257.174
175: JP6.15, PGA257.175
176: JP6.16, PGA257.176
177: JP6.17, PGA257.177
178: JP6.18, PGA257.178
179: JP6.19, PGA257.179
180: JP6.20, PGA257.180
181: JP6.21, PGA257.181
182: JP6.22, PGA257.182
183: JP6.23, PGA257.183
184: JP6.24, PGA257.184
185: JP6.25, PGA257.185
186: JP6.26, PGA257.186
187: JP6.27, PGA257.187
188: JP6.28, PGA257.188
189: JP6.29, PGA257.189
190: JP6.30, PGA257.190
191: JP6.31, PGA257.191
192: JP6.32, PGA257.192
193: JP7.1, PGA257.193
194: JP7.2, PGA257.194
195: JP7.3, PGA257.195
196: JP7.4, PGA257.196
197: JP7.5, PGA257.197
198: JP7.6, PGA257.198
199: JP7.7, PGA257.199
200: JP7.8, PGA257.200
201: JP7.9, PGA257.201
202: JP7.10, PGA257.202
203: JP7.11, PGA257.203
204: JP7.12, PGA257.204
205: JP7.13, PGA257.205
206: JP7.14, PGA257.206
207: JP7.15, PGA257.207
208: JP7.16, PGA257.208
209: JP7.17, PGA257.209
210: JP7.18, PGA257.210
211: JP7.19, PGA257.211
212: JP7.20, PGA257.212
213: JP7.21, PGA257.213
214: JP7.22, PGA257.214
215: JP7.23, PGA257.215
216: JP7.24, PGA257.216
217: JP7.25, PGA257.217
218: JP7.26, PGA257.218
219: JP7.27, PGA257.219
220: JP7.28, PGA257.220
221: JP7.29, PGA257.221
222: JP7.30, PGA257.222
223: JP7.31, PGA257.223
224: JP7.32, PGA257.224
225: JP8.1, PGA257.225
226: JP8.2, PGA257.226
227: JP8.3, PGA257.227
228: JP8.4, PGA257.228
229: JP8.5, PGA257.229
230: JP8.6, PGA257.230
231: JP8.7, PGA257.231
232: JP8.8, PGA257.232
233: JP8.9, PGA257.233
234: JP8.10, PGA257.234
235: JP8.11, PGA257.235
236: JP8.12, PGA257.236
237: JP8.13, PGA257.237
238: JP8.14, PGA257.238
239: JP8.15, PGA257.239
240: JP8.16, PGA257.240
241: JP8.17, PGA257.241
242: JP8.18, PGA257.242
243: JP8.19, PGA257.243
244: JP8.20, PGA257.244
245: JP8.21, PGA257.245
246: JP8.22, PGA257.246
247: JP8.23, PGA257.247
248: JP8.24, PGA257.248
249: JP8.25, PGA257.249
250: JP8.26, PGA257.250
251: JP8.27, PGA257.251
252: JP8.28, PGA257.252
253: JP8.29, PGA257.253
254: JP8.30, PGA257.254
255: JP8.31, PGA257.255
256: JP8.32, PGA257.256
257: PGA257.257

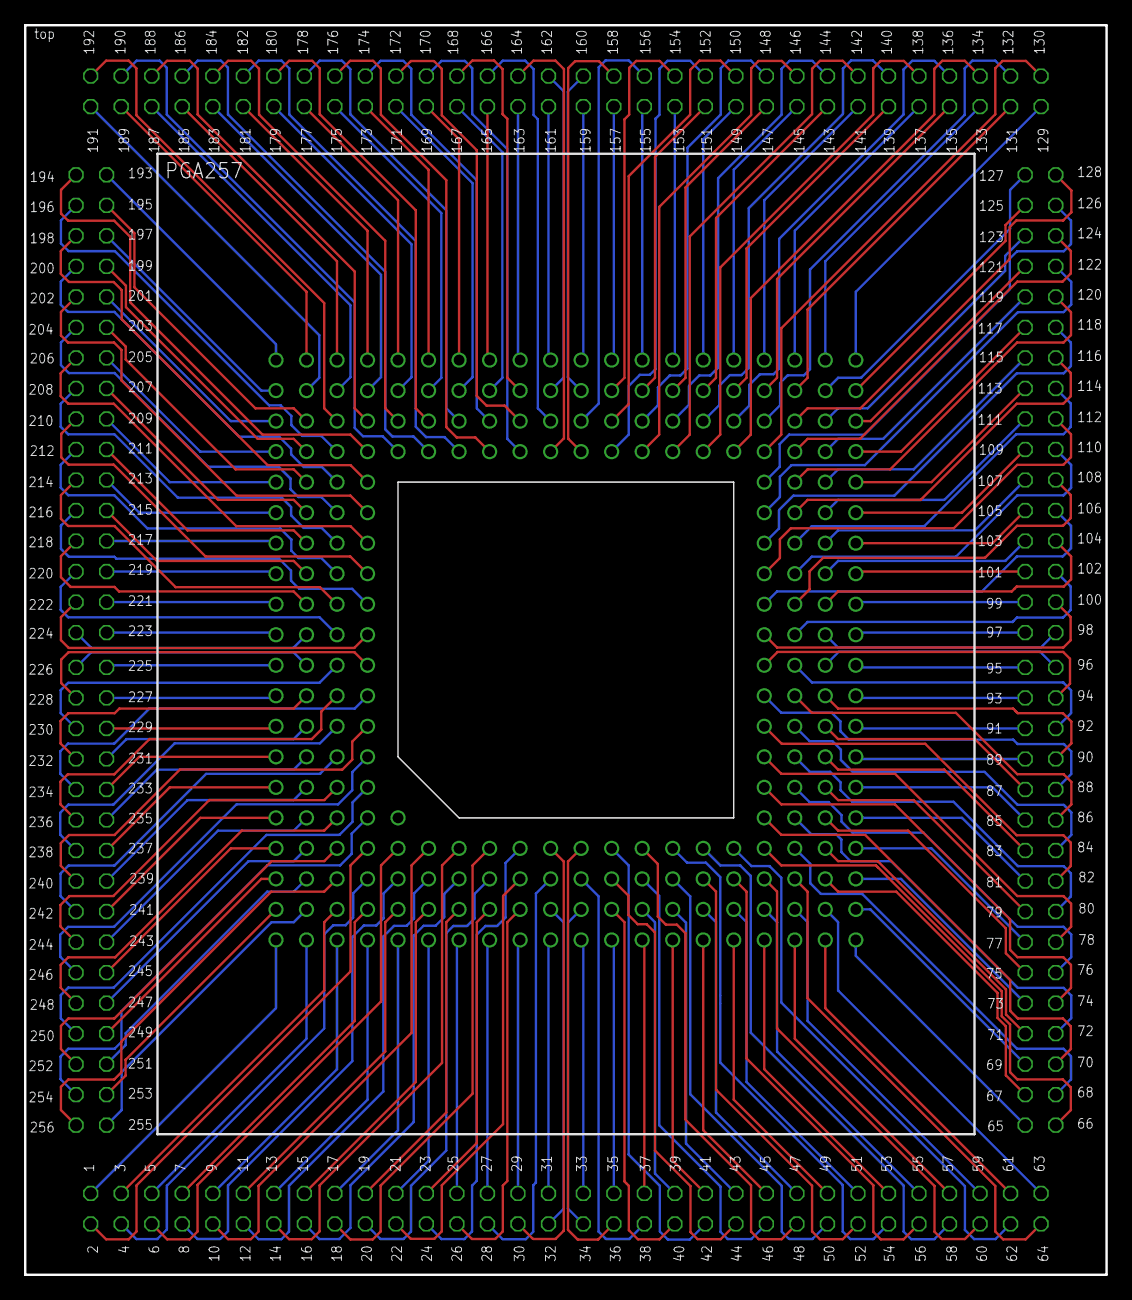
[picture p91: board PGA257_socket.brd from above]

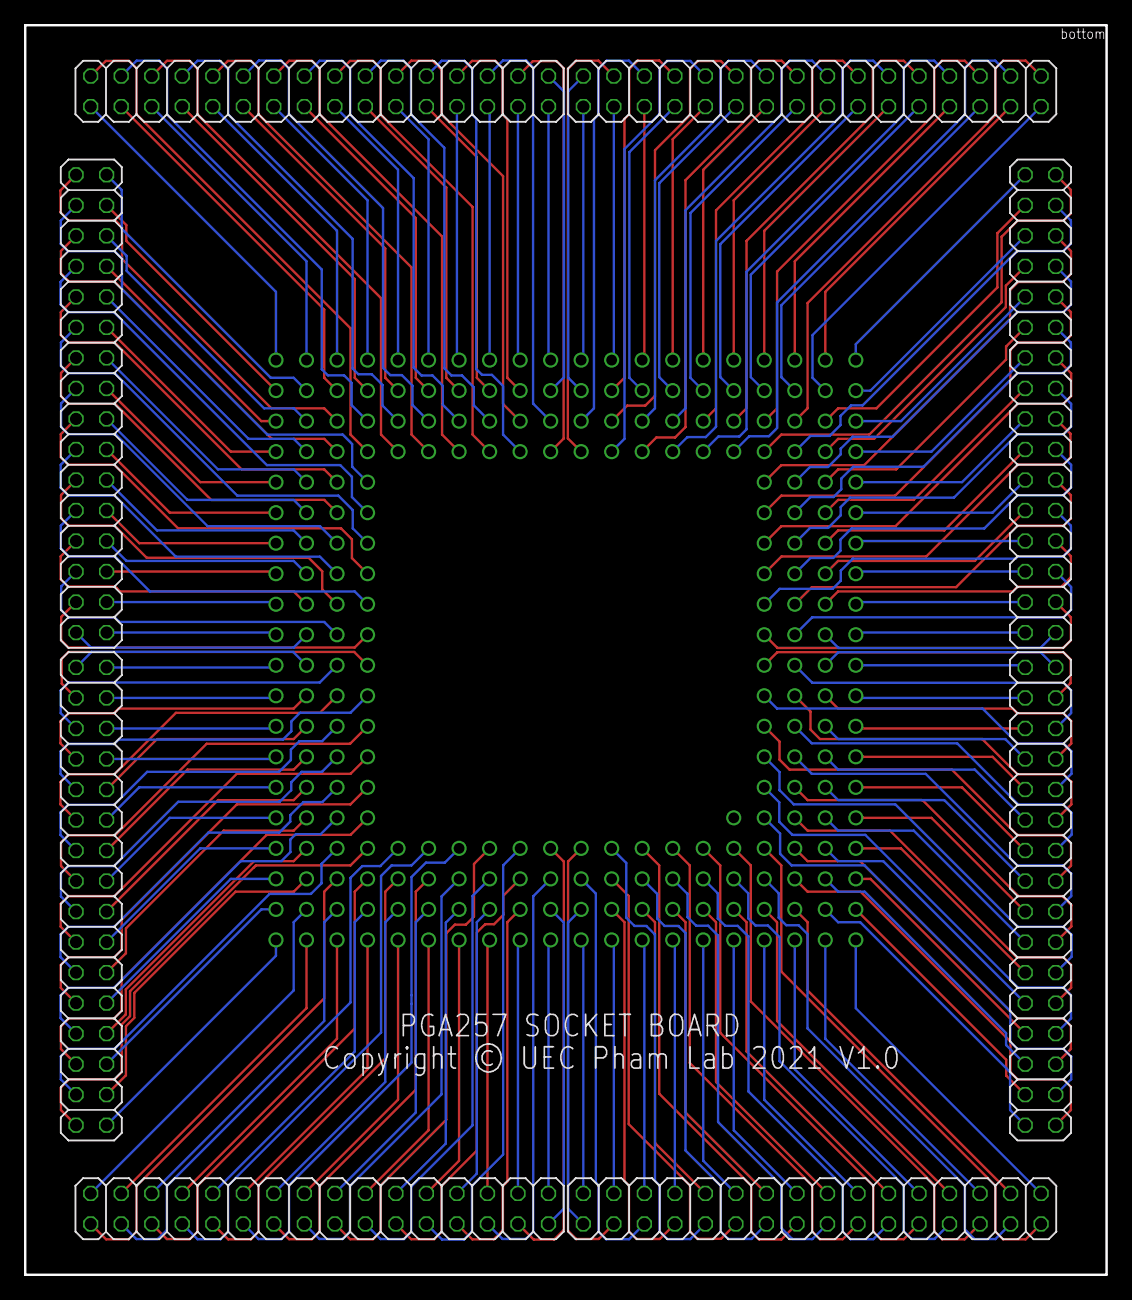
[picture p92: board PGA257_socket.brd from below]

Board: 2 copper layers, 90.0 x 104.0 mm, 9 parts (8 on the bottom side), 256 nets.
