Khaiduy/Open8_PCB/qfp160_socket.brd

## EAGLE design qfp160_socket.brd (2021-07-06)

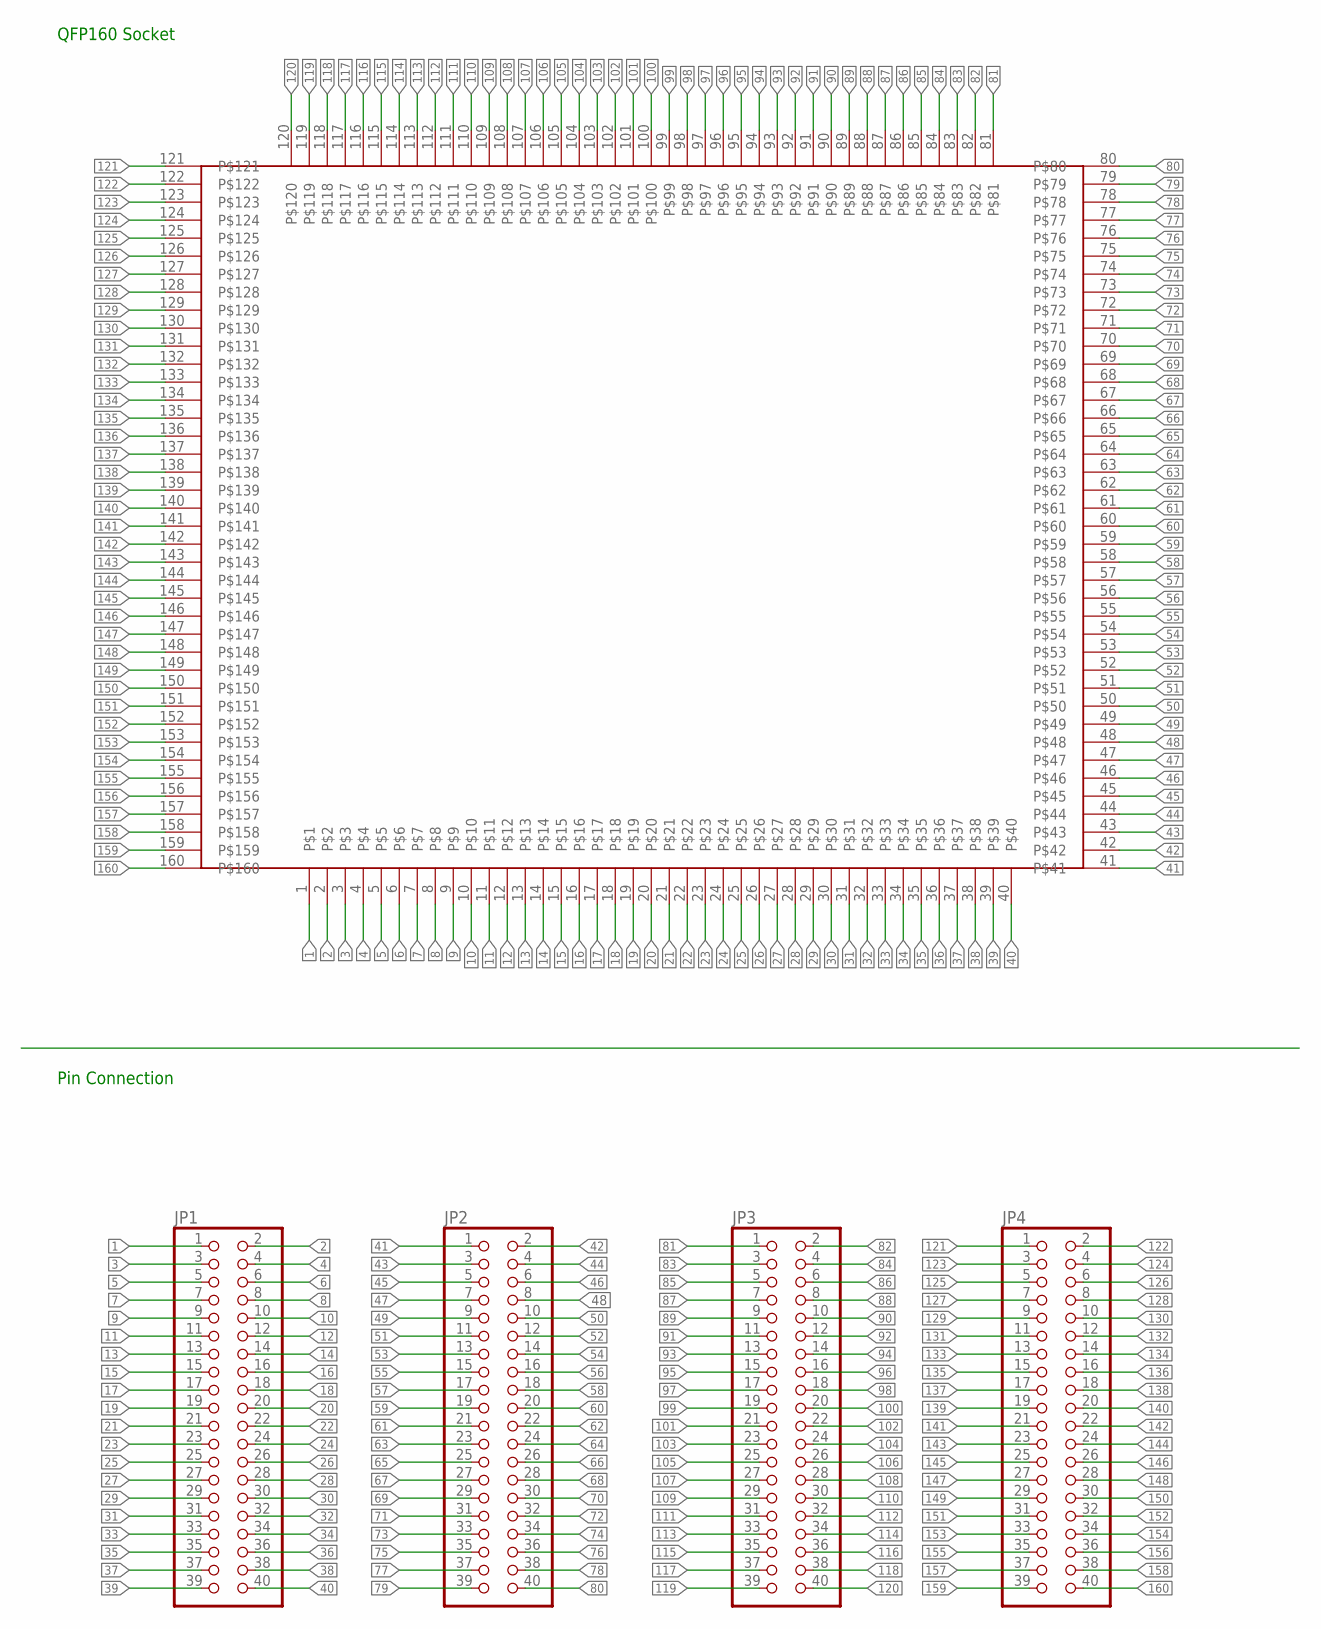
[picture p93: schematic qfp160_socket.sch]

Parts:
JP1, JP2, JP3, JP4: PINHD-2X20; 2X20
U$1: QFP160_SOCKET

Connections:
1: JP1.1, U$1.1
2: JP1.2, U$1.2
3: JP1.3, U$1.3
4: JP1.4, U$1.4
5: JP1.5, U$1.5
6: JP1.6, U$1.6
7: JP1.7, U$1.7
8: JP1.8, U$1.8
9: JP1.9, U$1.9
10: JP1.10, U$1.10
11: JP1.11, U$1.11
12: JP1.12, U$1.12
13: JP1.13, U$1.13
14: JP1.14, U$1.14
15: JP1.15, U$1.15
16: JP1.16, U$1.16
17: JP1.17, U$1.17
18: JP1.18, U$1.18
19: JP1.19, U$1.19
20: JP1.20, U$1.20
21: JP1.21, U$1.21
22: JP1.22, U$1.22
23: JP1.23, U$1.23
24: JP1.24, U$1.24
25: JP1.25, U$1.25
26: JP1.26, U$1.26
27: JP1.27, U$1.27
28: JP1.28, U$1.28
29: JP1.29, U$1.29
30: JP1.30, U$1.30
31: JP1.31, U$1.31
32: JP1.32, U$1.32
33: JP1.33, U$1.33
34: JP1.34, U$1.34
35: JP1.35, U$1.35
36: JP1.36, U$1.36
37: JP1.37, U$1.37
38: JP1.38, U$1.38
39: JP1.39, U$1.39
40: JP1.40, U$1.40
41: JP2.1, U$1.41
42: JP2.2, U$1.42
43: JP2.3, U$1.43
44: JP2.4, U$1.44
45: JP2.5, U$1.45
46: JP2.6, U$1.46
47: JP2.7, U$1.47
48: JP2.8, U$1.48
49: JP2.9, U$1.49
50: JP2.10, U$1.50
51: JP2.11, U$1.51
52: JP2.12, U$1.52
53: JP2.13, U$1.53
54: JP2.14, U$1.54
55: JP2.15, U$1.55
56: JP2.16, U$1.56
57: JP2.17, U$1.57
58: JP2.18, U$1.58
59: JP2.19, U$1.59
60: JP2.20, U$1.60
61: JP2.21, U$1.61
62: JP2.22, U$1.62
63: JP2.23, U$1.63
64: JP2.24, U$1.64
65: JP2.25, U$1.65
66: JP2.26, U$1.66
67: JP2.27, U$1.67
68: JP2.28, U$1.68
69: JP2.29, U$1.69
70: JP2.30, U$1.70
71: JP2.31, U$1.71
72: JP2.32, U$1.72
73: JP2.33, U$1.73
74: JP2.34, U$1.74
75: JP2.35, U$1.75
76: JP2.36, U$1.76
77: JP2.37, U$1.77
78: JP2.38, U$1.78
79: JP2.39, U$1.79
80: JP2.40, U$1.80
81: JP3.1, U$1.81
82: JP3.2, U$1.82
83: JP3.3, U$1.83
84: JP3.4, U$1.84
85: JP3.5, U$1.85
86: JP3.6, U$1.86
87: JP3.7, U$1.87
88: JP3.8, U$1.88
89: JP3.9, U$1.89
90: JP3.10, U$1.90
91: JP3.11, U$1.91
92: JP3.12, U$1.92
93: JP3.13, U$1.93
94: JP3.14, U$1.94
95: JP3.15, U$1.95
96: JP3.16, U$1.96
97: JP3.17, U$1.97
98: JP3.18, U$1.98
99: JP3.19, U$1.99
100: JP3.20, U$1.100
101: JP3.21, U$1.101
102: JP3.22, U$1.102
103: JP3.23, U$1.103
104: JP3.24, U$1.104
105: JP3.25, U$1.105
106: JP3.26, U$1.106
107: JP3.27, U$1.107
108: JP3.28, U$1.108
109: JP3.29, U$1.109
110: JP3.30, U$1.110
111: JP3.31, U$1.111
112: JP3.32, U$1.112
113: JP3.33, U$1.113
114: JP3.34, U$1.114
115: JP3.35, U$1.115
116: JP3.36, U$1.116
117: JP3.37, U$1.117
118: JP3.38, U$1.118
119: JP3.39, U$1.119
120: JP3.40, U$1.120
121: JP4.1, U$1.121
122: JP4.2, U$1.122
123: JP4.3, U$1.123
124: JP4.4, U$1.124
125: JP4.5, U$1.125
126: JP4.6, U$1.126
127: JP4.7, U$1.127
128: JP4.8, U$1.128
129: JP4.9, U$1.129
130: JP4.10, U$1.130
131: JP4.11, U$1.131
132: JP4.12, U$1.132
133: JP4.13, U$1.133
134: JP4.14, U$1.134
135: JP4.15, U$1.135
136: JP4.16, U$1.136
137: JP4.17, U$1.137
138: JP4.18, U$1.138
139: JP4.19, U$1.139
140: JP4.20, U$1.140
141: JP4.21, U$1.141
142: JP4.22, U$1.142
143: JP4.23, U$1.143
144: JP4.24, U$1.144
145: JP4.25, U$1.145
146: JP4.26, U$1.146
147: JP4.27, U$1.147
148: JP4.28, U$1.148
149: JP4.29, U$1.149
150: JP4.30, U$1.150
151: JP4.31, U$1.151
152: JP4.32, U$1.152
153: JP4.33, U$1.153
154: JP4.34, U$1.154
155: JP4.35, U$1.155
156: JP4.36, U$1.156
157: JP4.37, U$1.157
158: JP4.38, U$1.158
159: JP4.39, U$1.159
160: JP4.40, U$1.160

Notes on the sheet:
QFP160 Socket
Pin Connection

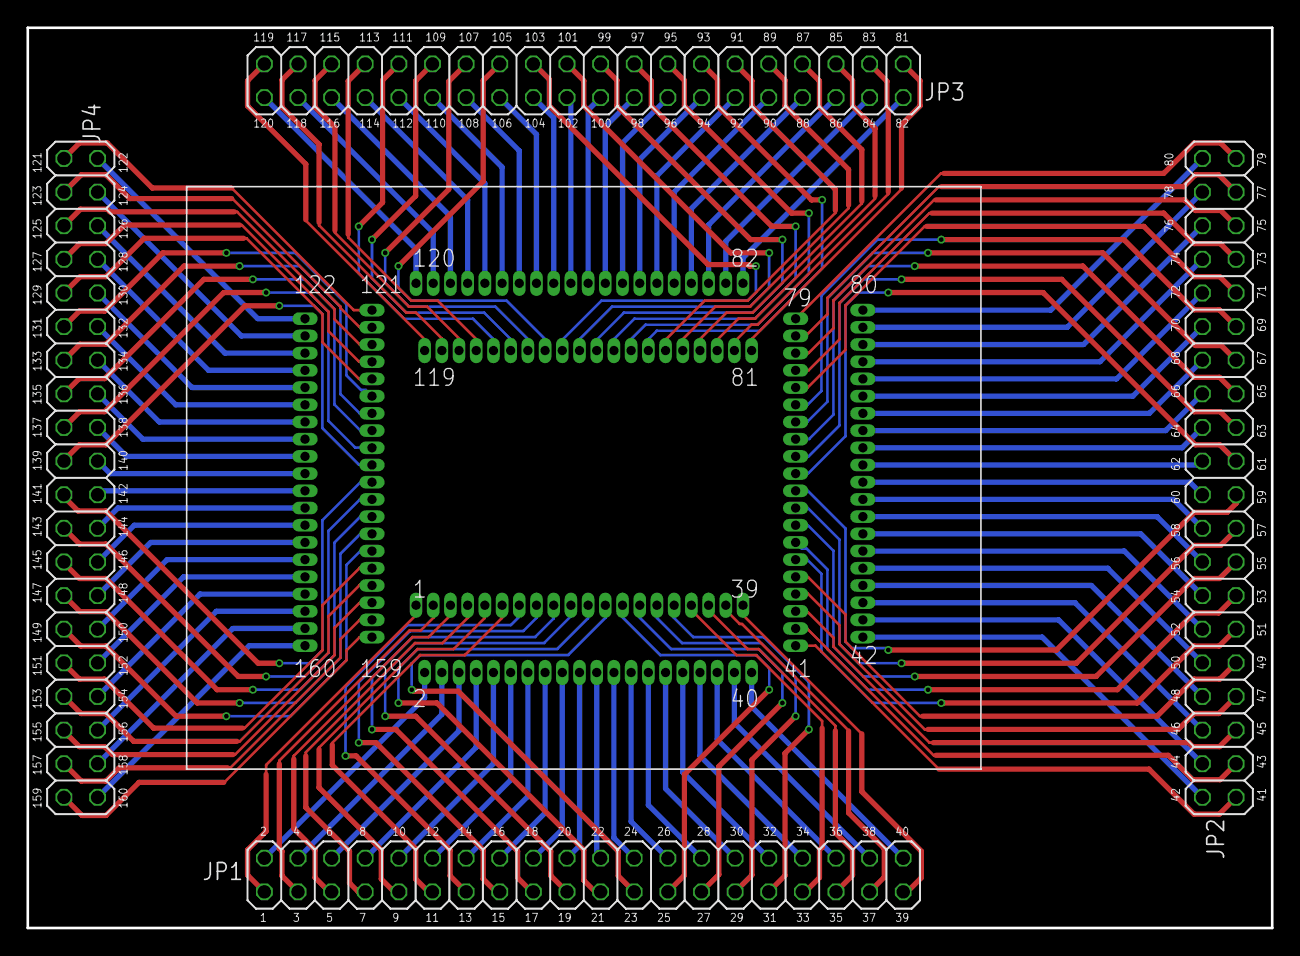
[picture p94: board qfp160_socket.brd from above]

Board: 2 copper layers, 94.0 x 68.0 mm, 5 parts (0 on the bottom side), 160 nets.
