Khaiduy/Open8_PCB/demo_open8.brd

## EAGLE design demo_open8.brd (2021-06-29)

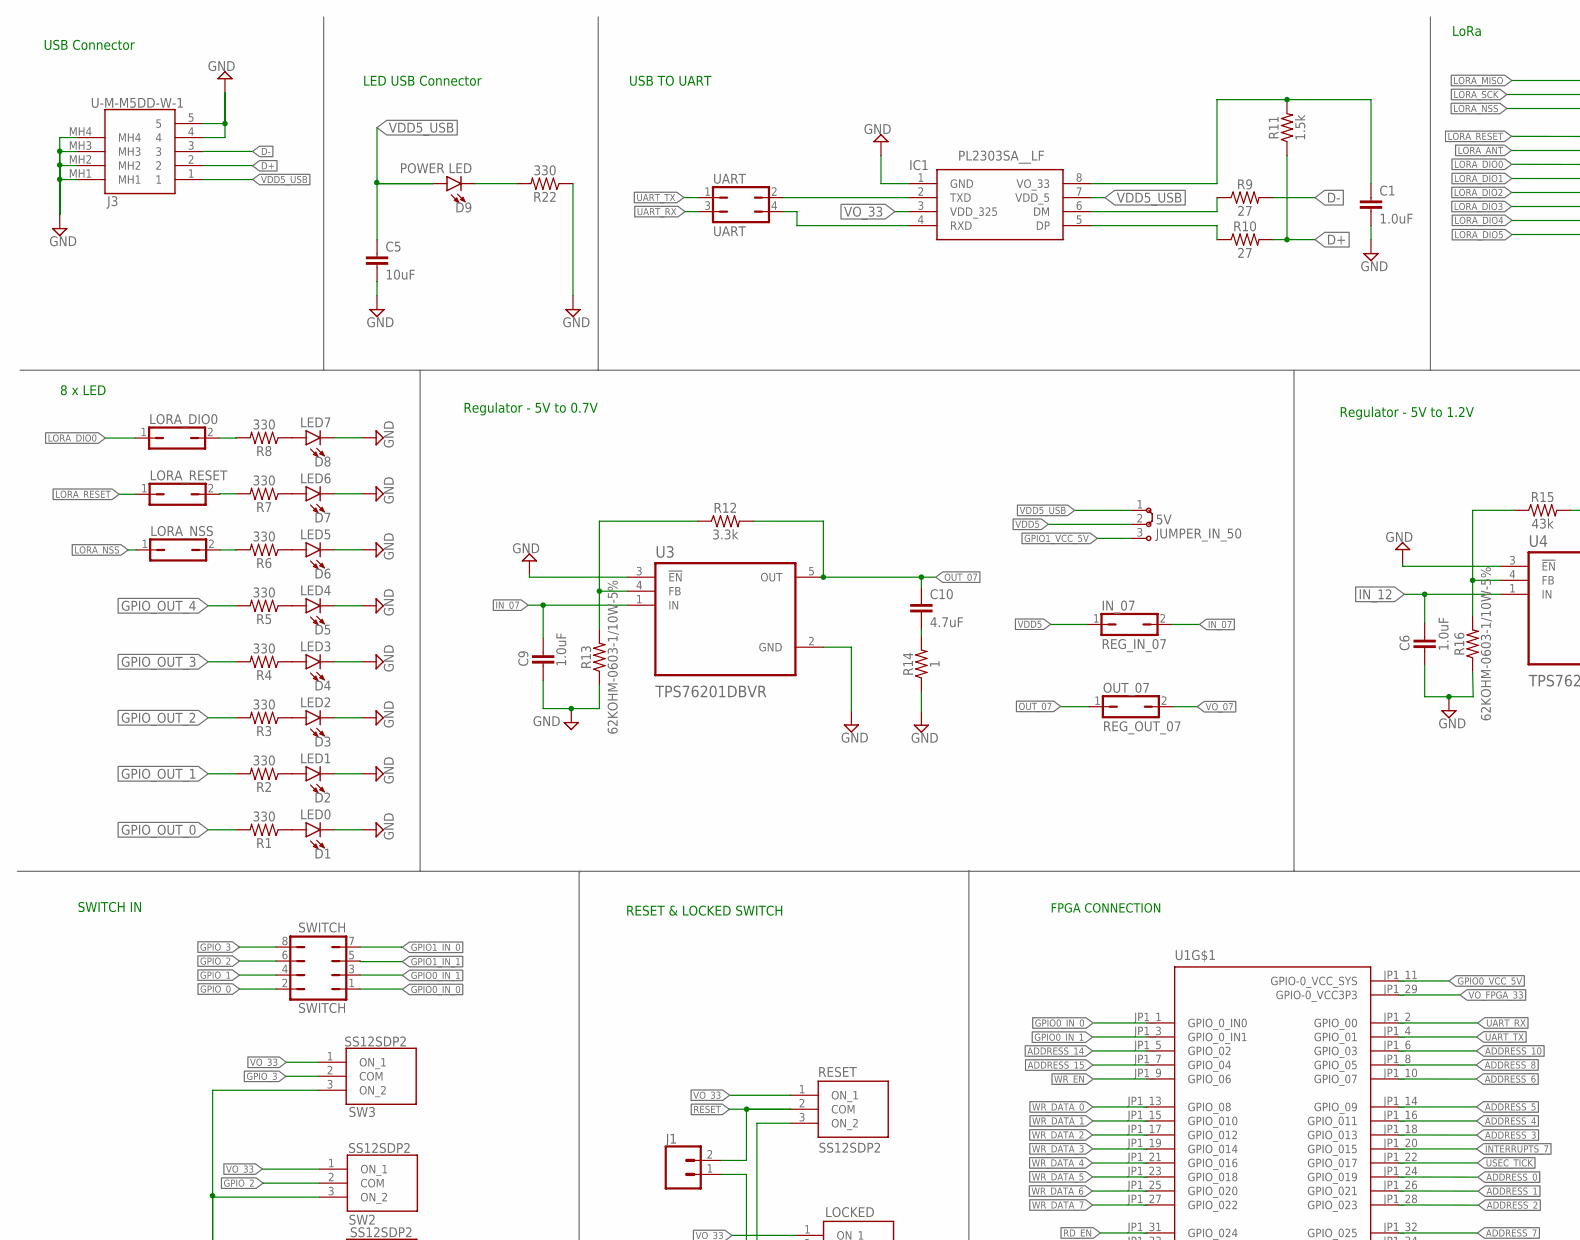
[picture p95: schematic demo_open8.sch, part in row 1, column 1]

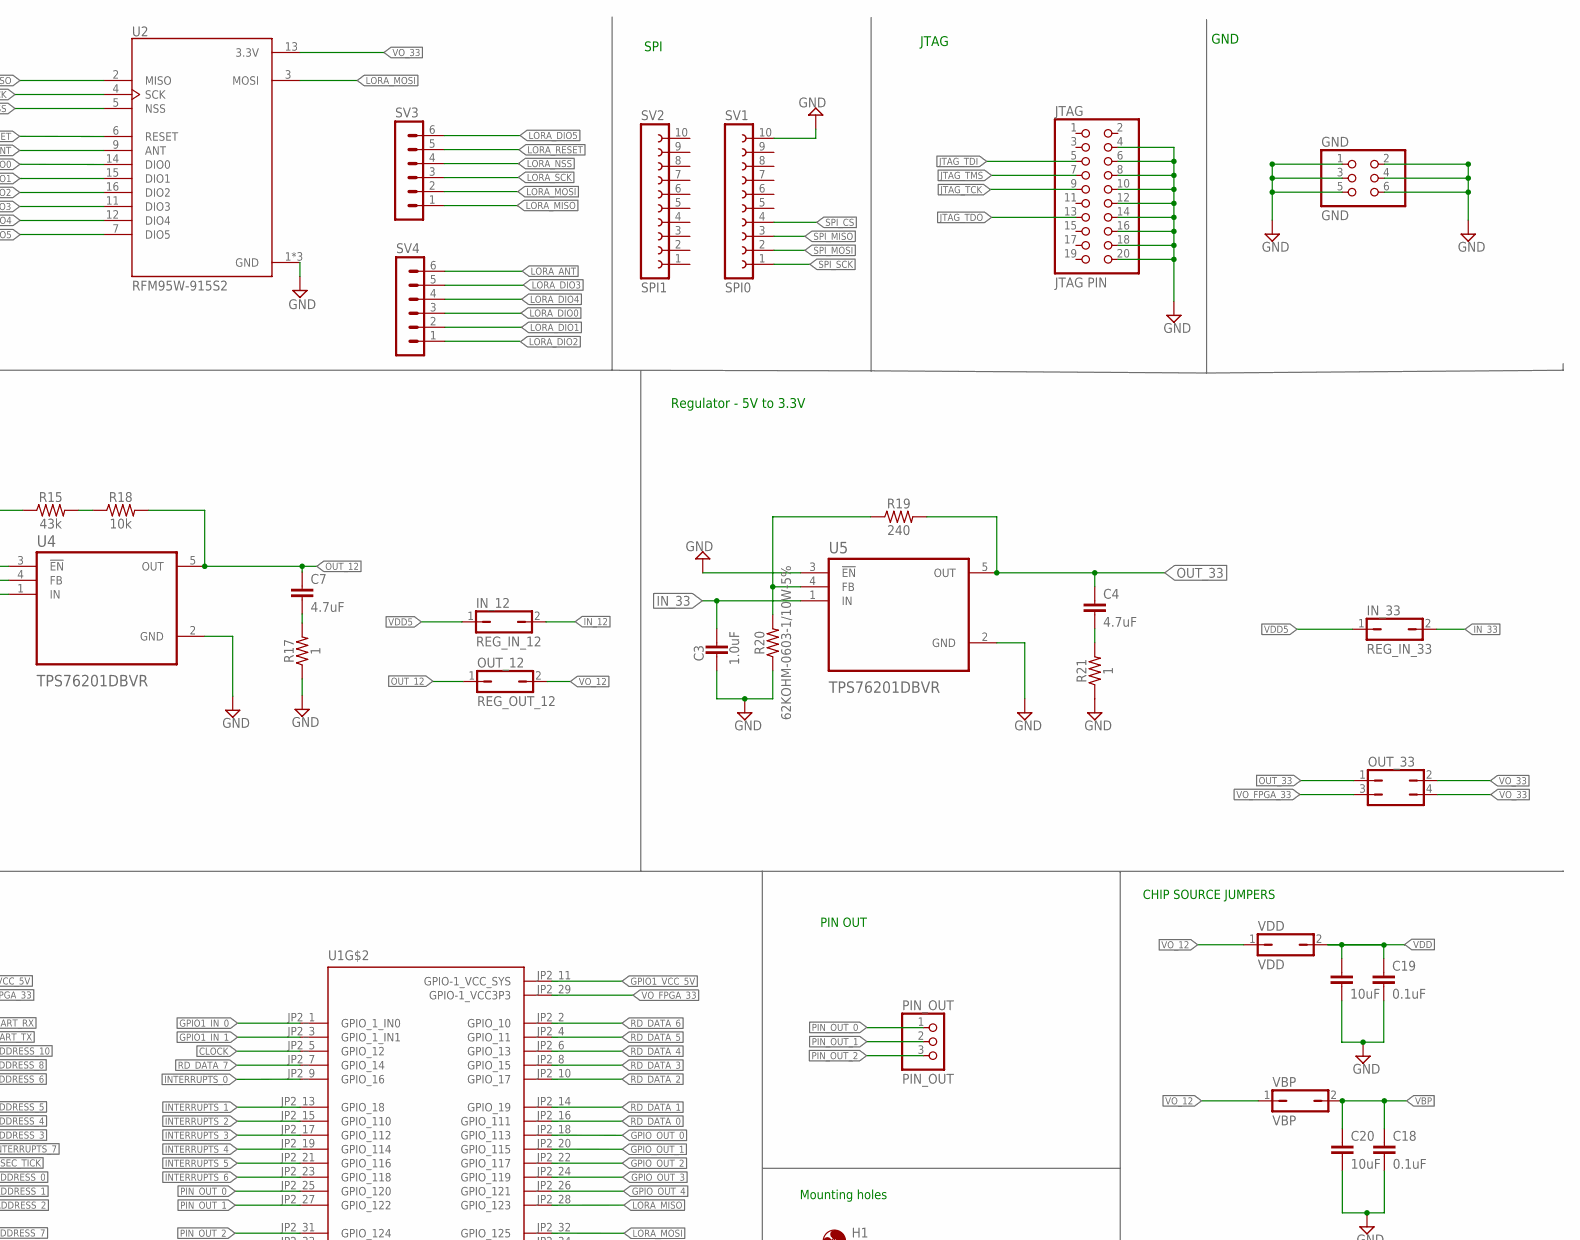
[picture p96: schematic demo_open8.sch, part in row 1, column 2]

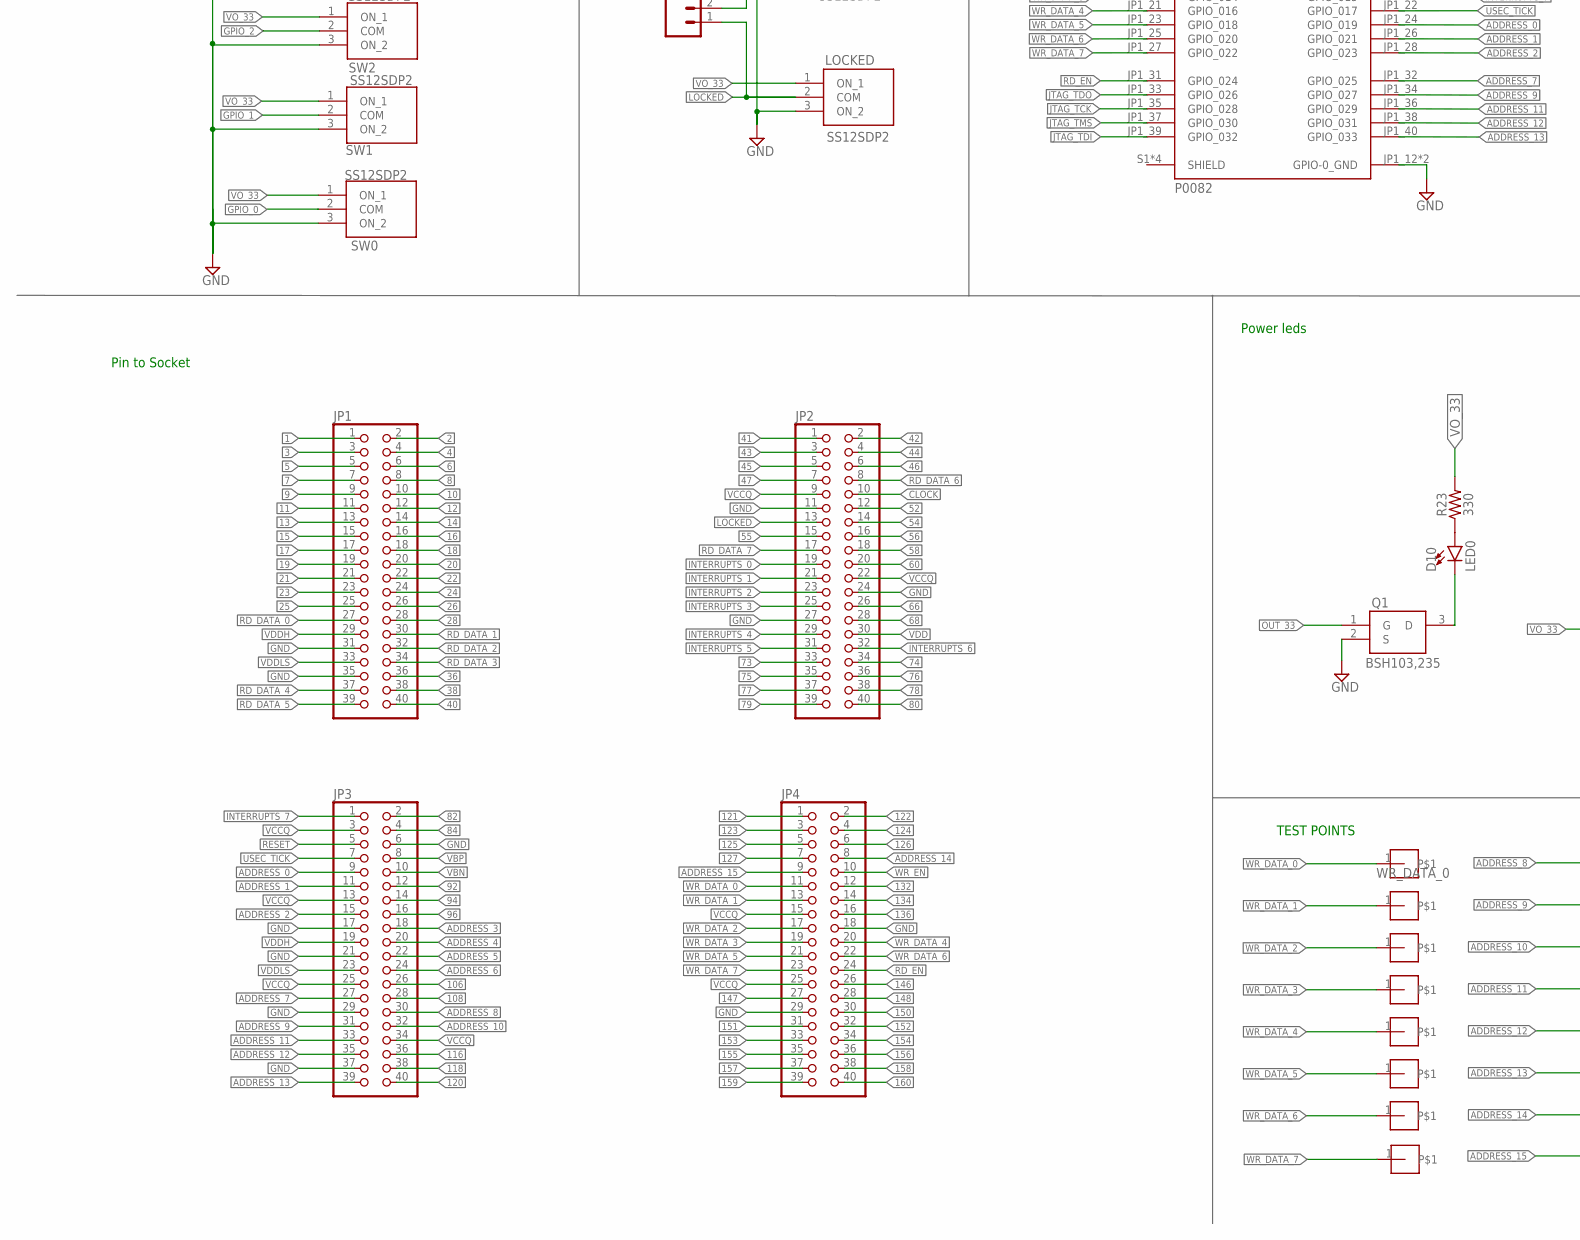
[picture p97: schematic demo_open8.sch, part in row 2, column 1]

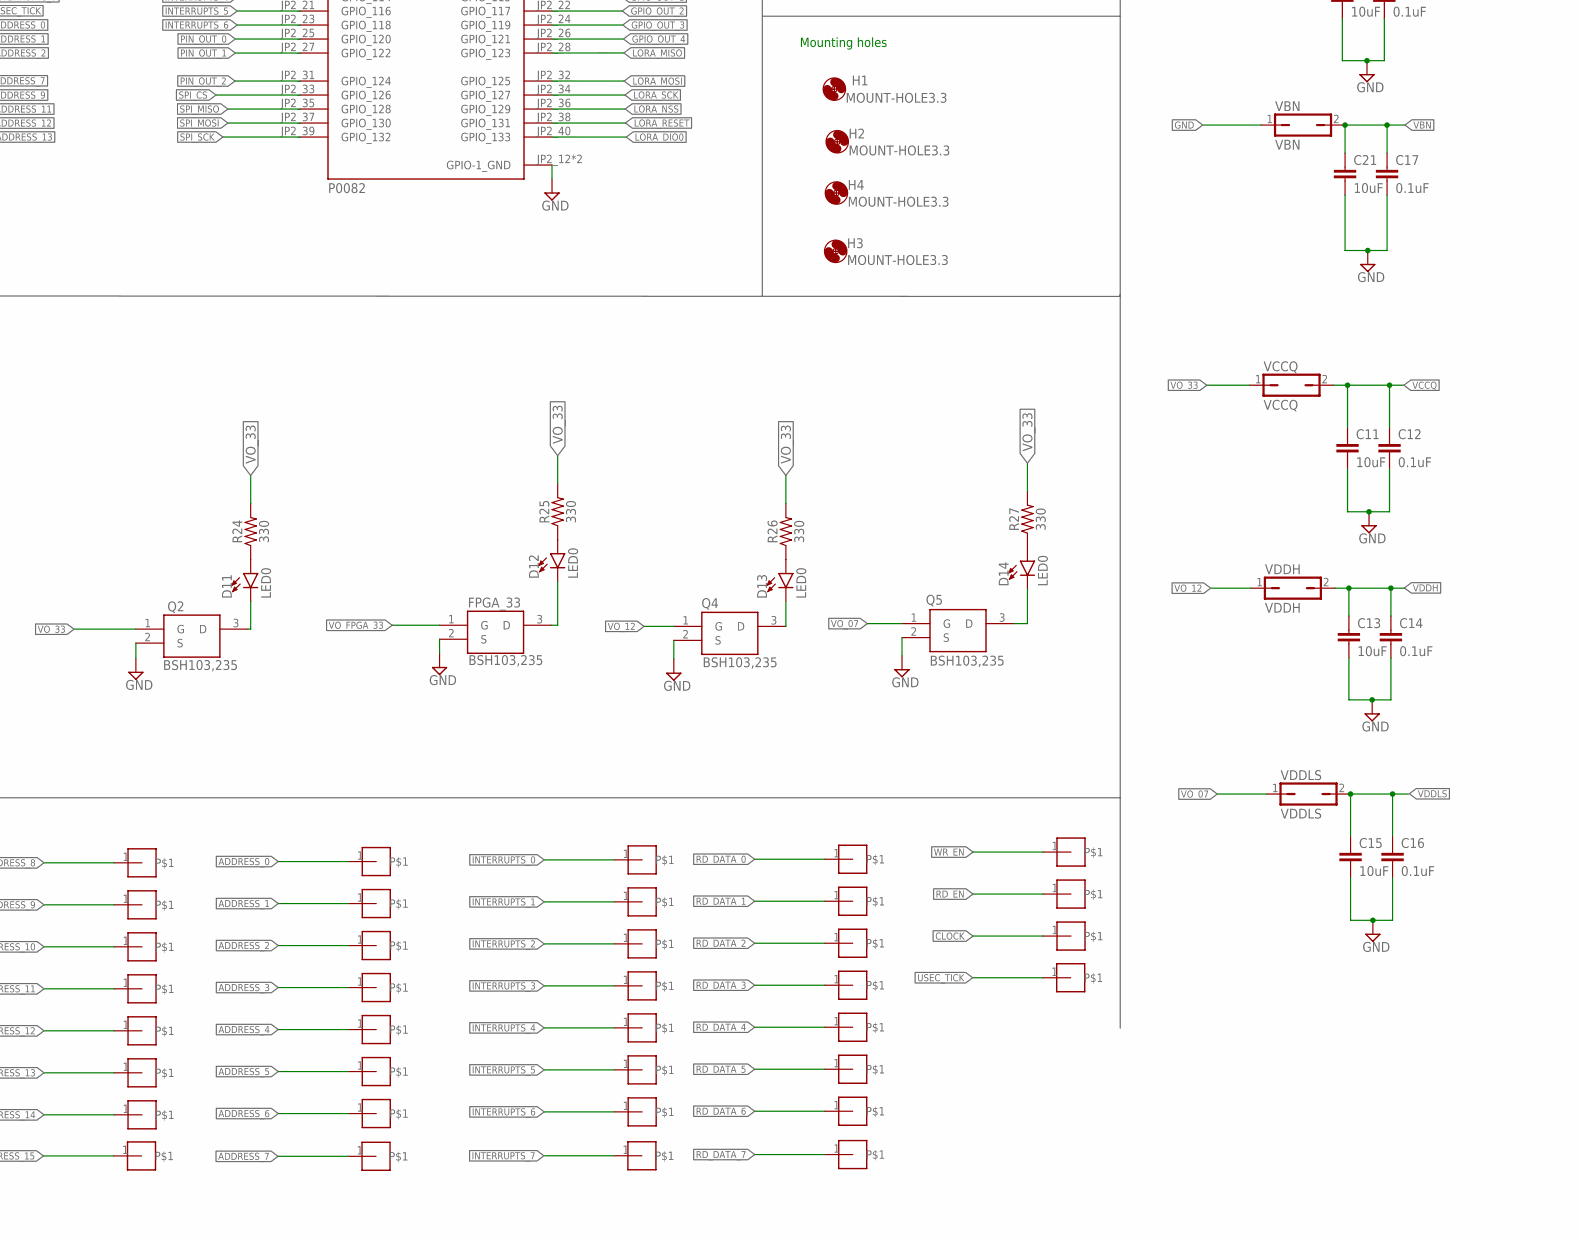
[picture p98: schematic demo_open8.sch, part in row 2, column 2]

Parts:
5V: JUMPER_IN_50; 04C
ADDRESS_0, ADDRESS_1, ADDRESS_2, ADDRESS_3, ADDRESS_4, ADDRESS_5, ADDRESS_6, ADDRESS_7, ADDRESS_8, ADDRESS_9, ADDRESS_10, ADDRESS_11, ADDRESS_12, ADDRESS_13, ADDRESS_14, ADDRESS_15: POINT
C1, C3, C6, C9: 1.0uF; 0603
C4, C7, C10: 4.7uF; 0603
C5, C11, C13, C15, C20, C21, C22: 10uF; 0603
C12, C14, C16, C17, C18, C19: 0.1uF; 0603
CLOCK: POINT
D1, D10, D11, D12, D13, D14: LED0; LED-0603
D2: LED1; LED-0603
D3: LED2; LED-0603
D4: LED3; LED-0603
D5: LED4; LED-0603
D6: LED5; LED-0603
D7: LED6; LED-0603
D8: LED7; LED-0603
D9: POWER LED; LED-0603
FPGA_33: BSH103,235; SOT95P230X110-3N
GND: GND; 2X03
H1, H2, H3, H4: MOUNT-HOLE3.3; 3,3
IC1: PL2303SA__LF; SOIC127P600X170-8N
INTERRUPTS_6: INTERRUPTS_6; POINT
IN_07: REG_IN_07; JP1
IN_12: REG_IN_12; JP1
IN_33: REG_IN_33; JP1
J1: CONN_02; 1X02
J3: U-M-M5DD-W-1; UMM5DDW1
JP1, JP2, JP3, JP4: PINHD-2X20; 2X20
JTAG: JTAG PIN; 2X10
LOCKED: SS12SDP2
LORA_DIO0: JP1Q; JP1
LORA_NSS: JP1Q; JP1
LORA_RESET: JP1Q; JP1
OUT_07: REG_OUT_07; JP1
OUT_12: REG_OUT_12; JP1
OUT_33: JP2Q
PIN_OUT: PIN_OUT; 1X03
Q1, Q2, Q4, Q5: BSH103,235; SOT95P230X110-3N
R1, R2, R3, R4, R5, R6, R7, R8, R22, R23, R24, R25, R26, R27: 330; 0603
R9, R10: 27; 0603
R11: 1.5k; 0603
R12: 3.3k; 0603
R13, R16, R20: 62KOHM-0603-1/10W-5%; 0603
R14, R17, R21: 1; 0603
R15: 43k; 0603
R18: 10k; 0603
R19: 240; 0603
RD_DATA_0, RD_DATA_2, RD_DATA_3, RD_DATA_4, RD_DATA_5, RD_DATA_6, RD_DATA_7: POINT
RD_EN: POINT
RESET: SS12SDP2
SV1: SPI0; FE10
SV2: SPI1; FE10
SV3, SV4: MA06-1
SW0, SW1, SW2, SW3: SS12SDP2
SWITCH: SWITCH; JP4Q
U1: P0082; MODULE_P0082_BOTTOMMOUNT
U2: RFM95W-915S2; XCVR_RFM95W-915S2
U3, U4, U5: TPS76201DBVR; SOT95P280X145-5N
U$4, U$40: POINT
U$10: INTERRUPTS_0; POINT
U$11: INTERRUPTS_1; POINT
U$12: INTERRUPTS_2; POINT
U$13: INTERRUPTS_3; POINT
U$14, U$15: INTERRUPTS_5; POINT
U$17: INTERRUPTS_7; POINT
UART: UART; JP2Q
USEC_TICK: POINT
VBN: VBN; JP1
VBP: VBP; JP1
VCCQ: VCCQ; JP1
VDD: VDD; JP1
VDDH: VDDH; JP1
VDDLS: VDDLS; JP1
WR_DATA_0, WR_DATA_1, WR_DATA_2, WR_DATA_3, WR_DATA_4, WR_DATA_5, WR_DATA_7: POINT
WR_EN: POINT

Connections:
1: JP1.1
2: JP1.2
3: JP1.3
4: JP1.4
5: JP1.5
6: JP1.6
7: JP1.7
8: JP1.8
9: JP1.9
10: JP1.10
11: JP1.11
12: JP1.12
13: JP1.13
14: JP1.14
15: JP1.15
16: JP1.16
17: JP1.17
18: JP1.18
19: JP1.19
20: JP1.20
21: JP1.21
22: JP1.22
23: JP1.23
24: JP1.24
25: JP1.25
26: JP1.26
28: JP1.28
36: JP1.36
38: JP1.38
40: JP1.40
41: JP2.1
42: JP2.2
43: JP2.3
44: JP2.4
45: JP2.5
46: JP2.6
47: JP2.7
52: JP2.12
54: JP2.14
55: JP2.15
56: JP2.16
58: JP2.18
60: JP2.20
66: JP2.26
68: JP2.28
73: JP2.33
74: JP2.34
75: JP2.35
76: JP2.36
77: JP2.37
78: JP2.38
79: JP2.39
80: JP2.40
82: JP3.2
84: JP3.4
92: JP3.12
94: JP3.14
96: JP3.16
106: JP3.26
108: JP3.28
116: JP3.36
118: JP3.38
120: JP3.40
121: JP4.1
122: JP4.2
123: JP4.3
124: JP4.4
125: JP4.5
126: JP4.6
127: JP4.7
132: JP4.12
134: JP4.14
136: JP4.16
146: JP4.26
147: JP4.27
148: JP4.28
150: JP4.30
151: JP4.31
152: JP4.32
153: JP4.33
154: JP4.34
155: JP4.35
156: JP4.36
157: JP4.37
158: JP4.38
159: JP4.39
160: JP4.40
ADDRESS_0: ADDRESS_0.1, JP3.9, U1.JP1_24 (GPIO_019)
ADDRESS_1: ADDRESS_1.1, JP3.11, U1.JP1_26 (GPIO_021)
ADDRESS_2: ADDRESS_2.1, JP3.15, U1.JP1_28 (GPIO_023)
ADDRESS_3: ADDRESS_3.1, JP3.18, U1.JP1_18 (GPIO_013)
ADDRESS_4: ADDRESS_4.1, JP3.20, U1.JP1_16 (GPIO_011)
ADDRESS_5: ADDRESS_5.1, JP3.22, U1.JP1_14 (GPIO_09)
ADDRESS_6: ADDRESS_6.1, JP3.24, U1.JP1_10 (GPIO_07)
ADDRESS_7: ADDRESS_7.1, JP3.27, U1.JP1_32 (GPIO_025)
ADDRESS_8: ADDRESS_8.1, JP3.30, U1.JP1_8 (GPIO_05)
ADDRESS_9: ADDRESS_9.1, JP3.31, U1.JP1_34 (GPIO_027)
ADDRESS_10: ADDRESS_10.1, JP3.32, U1.JP1_6 (GPIO_03)
ADDRESS_11: ADDRESS_11.1, JP3.33, U1.JP1_36 (GPIO_029)
ADDRESS_12: ADDRESS_12.1, JP3.35, U1.JP1_38 (GPIO_031)
ADDRESS_13: ADDRESS_13.1, JP3.39, U1.JP1_40 (GPIO_033)
ADDRESS_14: ADDRESS_14.1, JP4.8, U1.JP1_5 (GPIO_02)
ADDRESS_15: ADDRESS_15.1, JP4.9, U1.JP1_7 (GPIO_04)
CLOCK: CLOCK.1, JP2.10, U1.JP2_5 (GPIO_12)
D+: J3.2, R10.2, R11.1
D-: J3.3, R9.2
GND: C1.2, C3.2, C5.2, C6.2, C9.2, C11.2, C12.2, C13.2, C14.2, C15.2, C16.2, C17.2, C18.2, C19.2, C20.2, C21.2, C22.2, D1.C, D2.C, D3.C, D4.C, D5.C, D6.C, D7.C, D8.C, FPGA_33.2 (S), GND.1, GND.2, GND.3, GND.4, GND.5, GND.6, IC1.1 (GND), J3.4, J3.5, J3.MH1, J3.MH2, J3.MH3, J3.MH4, JP1.31, JP1.35, JP2.11, JP2.24, JP2.27, JP3.6, JP3.17, JP3.21, JP3.29, JP3.37, JP4.18, JP4.29, JTAG.4, JTAG.6, JTAG.8, JTAG.10, JTAG.12, JTAG.14, JTAG.16, JTAG.18, JTAG.20, LOCKED.3 (ON_2), Q1.2 (S), Q2.2 (S), Q4.2 (S), Q5.2 (S), R13.1, R14.1, R16.1, R17.1, R20.1, R21.1, R22.1, RESET.3 (ON_2), SV1.10, SW0.3 (ON_2), SW1.3 (ON_2), SW2.3 (ON_2), SW3.3 (ON_2), U1.JP1_12 (GPIO-0_GND), U1.JP1_30 (GPIO-0_GND), U1.JP2_12 (GPIO-1_GND), U1.JP2_30 (GPIO-1_GND), U2.1 (GND), U2.8 (GND), U2.10 (GND), U3.2 (GND), U3.3 (!EN), U4.2 (GND), U4.3 (!EN), U5.2 (GND), U5.3 (!EN), VBN.1
GPIO0_IN_0: SWITCH.1, U1.JP1_1 (GPIO_0_IN0)
GPIO0_IN_1: SWITCH.3, U1.JP1_3 (GPIO_0_IN1)
GPIO0_VCC_5V: U1.JP1_11 (GPIO-0_VCC_SYS)
GPIO1_IN_0: SWITCH.7, U1.JP2_1 (GPIO_1_IN0)
GPIO1_IN_1: SWITCH.5, U1.JP2_3 (GPIO_1_IN1)
GPIO1_VCC_5V: 5V.3, U1.JP2_11 (GPIO-1_VCC_SYS)
GPIO_0: SW0.2 (COM), SWITCH.2
GPIO_1: SW1.2 (COM), SWITCH.4
GPIO_2: SW2.2 (COM), SWITCH.6
GPIO_3: SW3.2 (COM), SWITCH.8
GPIO_OUT_0: R1.2, U1.JP2_18 (GPIO_113)
GPIO_OUT_1: R2.2, U1.JP2_20 (GPIO_115)
GPIO_OUT_2: R3.2, U1.JP2_22 (GPIO_117)
GPIO_OUT_3: R4.2, U1.JP2_24 (GPIO_119)
GPIO_OUT_4: R5.2, U1.JP2_26 (GPIO_121)
INTERRUPTS_0: JP2.19, U1.JP2_9 (GPIO_16), U$10.1
INTERRUPTS_1: JP2.21, U1.JP2_13 (GPIO_18), U$11.1
INTERRUPTS_2: JP2.23, U1.JP2_15 (GPIO_110), U$12.1
INTERRUPTS_3: JP2.25, U1.JP2_17 (GPIO_112), U$13.1
INTERRUPTS_4: JP2.29, U1.JP2_19 (GPIO_114), U$14.1
INTERRUPTS_5: JP2.31, U1.JP2_21 (GPIO_116), U$15.1
INTERRUPTS_6: INTERRUPTS_6.1, JP2.32, U1.JP2_23 (GPIO_118)
INTERRUPTS_7: JP3.1, U1.JP1_20 (GPIO_015), U$17.1
IN_07: C9.1, IN_07.2, U3.1 (IN)
IN_12: C6.1, IN_12.2, U4.1 (IN)
IN_33: C3.1, IN_33.2, U5.1 (IN)
JTAG_TCK: JTAG.9, U1.JP1_35 (GPIO_028)
JTAG_TDI: JTAG.5, U1.JP1_39 (GPIO_032)
JTAG_TDO: JTAG.13, U1.JP1_33 (GPIO_026)
JTAG_TMS: JTAG.7, U1.JP1_37 (GPIO_030)
LOCKED: J1.1, JP2.13, LOCKED.2 (COM)
LORA_ANT: SV4.6, U2.9 (ANT)
LORA_DIO0: LORA_DIO0.1, SV4.3, U1.JP2_40 (GPIO_133), U2.14 (DIO0)
LORA_DIO1: SV4.2, U2.15 (DIO1)
LORA_DIO2: SV4.1, U2.16 (DIO2)
LORA_DIO3: SV4.5, U2.11 (DIO3)
LORA_DIO4: SV4.4, U2.12 (DIO4)
LORA_DIO5: SV3.6, U2.7 (DIO5)
LORA_MISO: SV3.1, U1.JP2_28 (GPIO_123), U2.2 (MISO)
LORA_MOSI: SV3.2, U1.JP2_32 (GPIO_125), U2.3 (MOSI)
LORA_NSS: LORA_NSS.1, SV3.4, U1.JP2_36 (GPIO_129), U2.5 (NSS)
LORA_RESET: LORA_RESET.1, SV3.5, U1.JP2_38 (GPIO_131), U2.6 (RESET)
LORA_SCK: SV3.3, U1.JP2_34 (GPIO_127), U2.4 (SCK)
unnamed: D1.A, R1.1
unnamed: D8.A, R8.1
unnamed: D7.A, R7.1
unnamed: D6.A, R6.1
unnamed: D5.A, R5.1
unnamed: D4.A, R4.1
unnamed: D2.A, R2.1
unnamed: D3.A, R3.1
unnamed: D10.A, R23.1
unnamed: D10.C, Q1.3 (D)
unnamed: D12.A, R25.1
unnamed: D12.C, FPGA_33.3 (D)
unnamed: D11.A, R24.1
unnamed: D11.C, Q2.3 (D)
unnamed: D13.A, R26.1
unnamed: D13.C, Q4.3 (D)
unnamed: IC1.6 (DM), R9.1
unnamed: D14.A, R27.1
unnamed: D14.C, Q5.3 (D)
unnamed: IC1.5 (DP), R10.1
unnamed: IC1.2 (TXD), UART.2
unnamed: IC1.4 (RXD), UART.4
unnamed: LORA_DIO0.2, R8.2
unnamed: LORA_RESET.2, R7.2
unnamed: LORA_NSS.2, R6.2
unnamed: R12.1, R13.2, U3.4 (FB)
unnamed: R15.1, R16.2, U4.4 (FB)
unnamed: C10.2, R14.2
unnamed: C7.2, R17.2
unnamed: R15.2, R18.1
unnamed: R19.1, R20.2, U5.4 (FB)
unnamed: C4.2, R21.2
unnamed: D9.C, R22.2
OUT_07: C10.1, OUT_07.1, R12.2, U3.5 (OUT)
OUT_12: C7.1, OUT_12.1, R18.2, U4.5 (OUT)
OUT_33: C4.1, OUT_33.1, Q1.1 (G), R19.2, U5.5 (OUT)
PIN_OUT_0: PIN_OUT.1, U1.JP2_25 (GPIO_120)
PIN_OUT_1: PIN_OUT.2, U1.JP2_27 (GPIO_122)
PIN_OUT_2: PIN_OUT.3, U1.JP2_31 (GPIO_124)
RD_DATA_0: JP1.27, RD_DATA_0.1, U1.JP2_16 (GPIO_111)
RD_DATA_1: JP1.30, U1.JP2_14 (GPIO_19), U$4.1
RD_DATA_2: JP1.32, RD_DATA_2.1, U1.JP2_10 (GPIO_17)
RD_DATA_3: JP1.34, RD_DATA_3.1, U1.JP2_8 (GPIO_15)
RD_DATA_4: JP1.37, RD_DATA_4.1, U1.JP2_6 (GPIO_13)
RD_DATA_5: JP1.39, RD_DATA_5.1, U1.JP2_4 (GPIO_11)
RD_DATA_6: JP2.8, RD_DATA_6.1, U1.JP2_2 (GPIO_10)
RD_DATA_7: JP2.17, RD_DATA_7.1, U1.JP2_7 (GPIO_14)
RD_EN: JP4.24, RD_EN.1, U1.JP1_31 (GPIO_024)
RESET: J1.2, JP3.5, RESET.2 (COM)
SPI_CS: SV1.4, U1.JP2_33 (GPIO_126)
SPI_MISO: SV1.3, U1.JP2_35 (GPIO_128)
SPI_MOSI: SV1.2, U1.JP2_37 (GPIO_130)
SPI_SCK: SV1.1, U1.JP2_39 (GPIO_132)
UART_RX: U1.JP1_2 (GPIO_00), UART.3
UART_TX: U1.JP1_4 (GPIO_01), UART.1
USEC_TICK: JP3.7, U1.JP1_22 (GPIO_017), USEC_TICK.1
VBN: C17.1, C21.1, JP3.10, VBN.2
VBP: C18.1, C20.1, JP3.8, VBP.2
VCCQ: C11.1, C12.1, JP2.9, JP2.22, JP3.3, JP3.13, JP3.25, JP3.34, JP4.15, JP4.25, VCCQ.2
VDD: C19.1, C22.1, JP2.30, VDD.2
VDD5: 5V.2, IN_07.1, IN_12.1, IN_33.1
VDD5_USB: 5V.1, C5.1, D9.A, IC1.7 (VDD_5), J3.1
VDDH: C13.1, C14.1, JP1.29, JP3.19, VDDH.2
VDDLS: C15.1, C16.1, JP1.33, JP3.23, VDDLS.2
VO_07: OUT_07.2, Q5.1 (G), VDDLS.1
VO_12: OUT_12.2, Q4.1 (G), VBP.1, VDD.1, VDDH.1
VO_33: C1.1, IC1.3 (VDD_325), IC1.8 (VO_33), LOCKED.1 (ON_1), OUT_33.2, OUT_33.4, Q2.1 (G), R11.2, R23.2, R24.2, R25.2, R26.2, R27.2, RESET.1 (ON_1), SW0.1 (ON_1), SW1.1 (ON_1), SW2.1 (ON_1), SW3.1 (ON_1), U2.13 (3.3V), VCCQ.1
VO_FPGA_33: FPGA_33.1 (G), OUT_33.3, U1.JP1_29 (GPIO-0_VCC3P3), U1.JP2_29 (GPIO-1_VCC3P3)
WR_DATA_0: JP4.11, U1.JP1_13 (GPIO_08), WR_DATA_0.1
WR_DATA_1: JP4.13, U1.JP1_15 (GPIO_010), WR_DATA_1.1
WR_DATA_2: JP4.17, U1.JP1_17 (GPIO_012), WR_DATA_2.1
WR_DATA_3: JP4.19, U1.JP1_19 (GPIO_014), WR_DATA_3.1
WR_DATA_4: JP4.20, U1.JP1_21 (GPIO_016), WR_DATA_4.1
WR_DATA_5: JP4.21, U1.JP1_23 (GPIO_018), WR_DATA_5.1
WR_DATA_6: JP4.22, U1.JP1_25 (GPIO_020), U$40.1
WR_DATA_7: JP4.23, U1.JP1_27 (GPIO_022), WR_DATA_7.1
WR_EN: JP4.10, U1.JP1_9 (GPIO_06), WR_EN.1

Notes on the sheet:
LED USB Connector
USB TO UART
8 x LED
Regulator - 5V to 0.7V
Regulator - 5V to 1.2V
Regulator - 5V to 3.3V
LoRa
SPI
JTAG
GND
SWITCH IN
RESET & LOCKED SWITCH
FPGA CONNECTION
PIN OUT
CHIP SOURCE JUMPERS
Pin to Socket
Mounting holes
Power leds
USB Connector
TEST POINTS

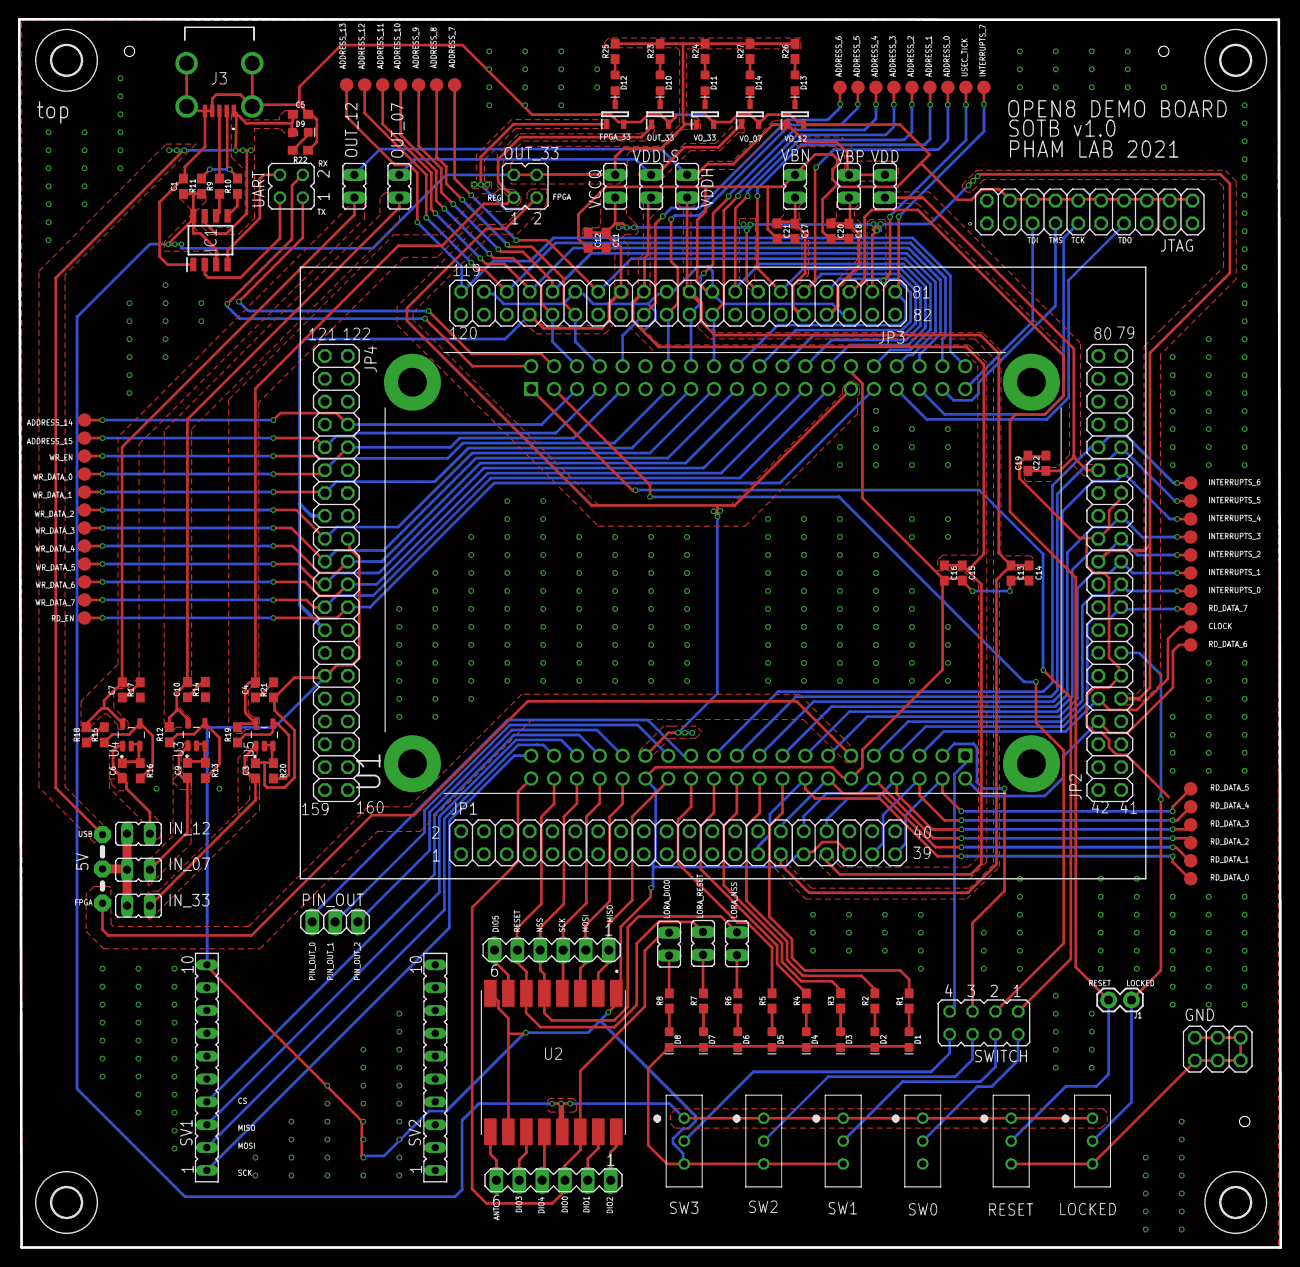
[picture p99: board demo_open8.brd from above]

Board: 2 copper layers, 140.2 x 136.6 mm, 157 parts (0 on the bottom side), 139 nets.
